ee23btech11217/Prism/PCB/Audio.kicad_sch

## KiCad design PCB/Audio.kicad_sch (2025-03-10, last stored version)

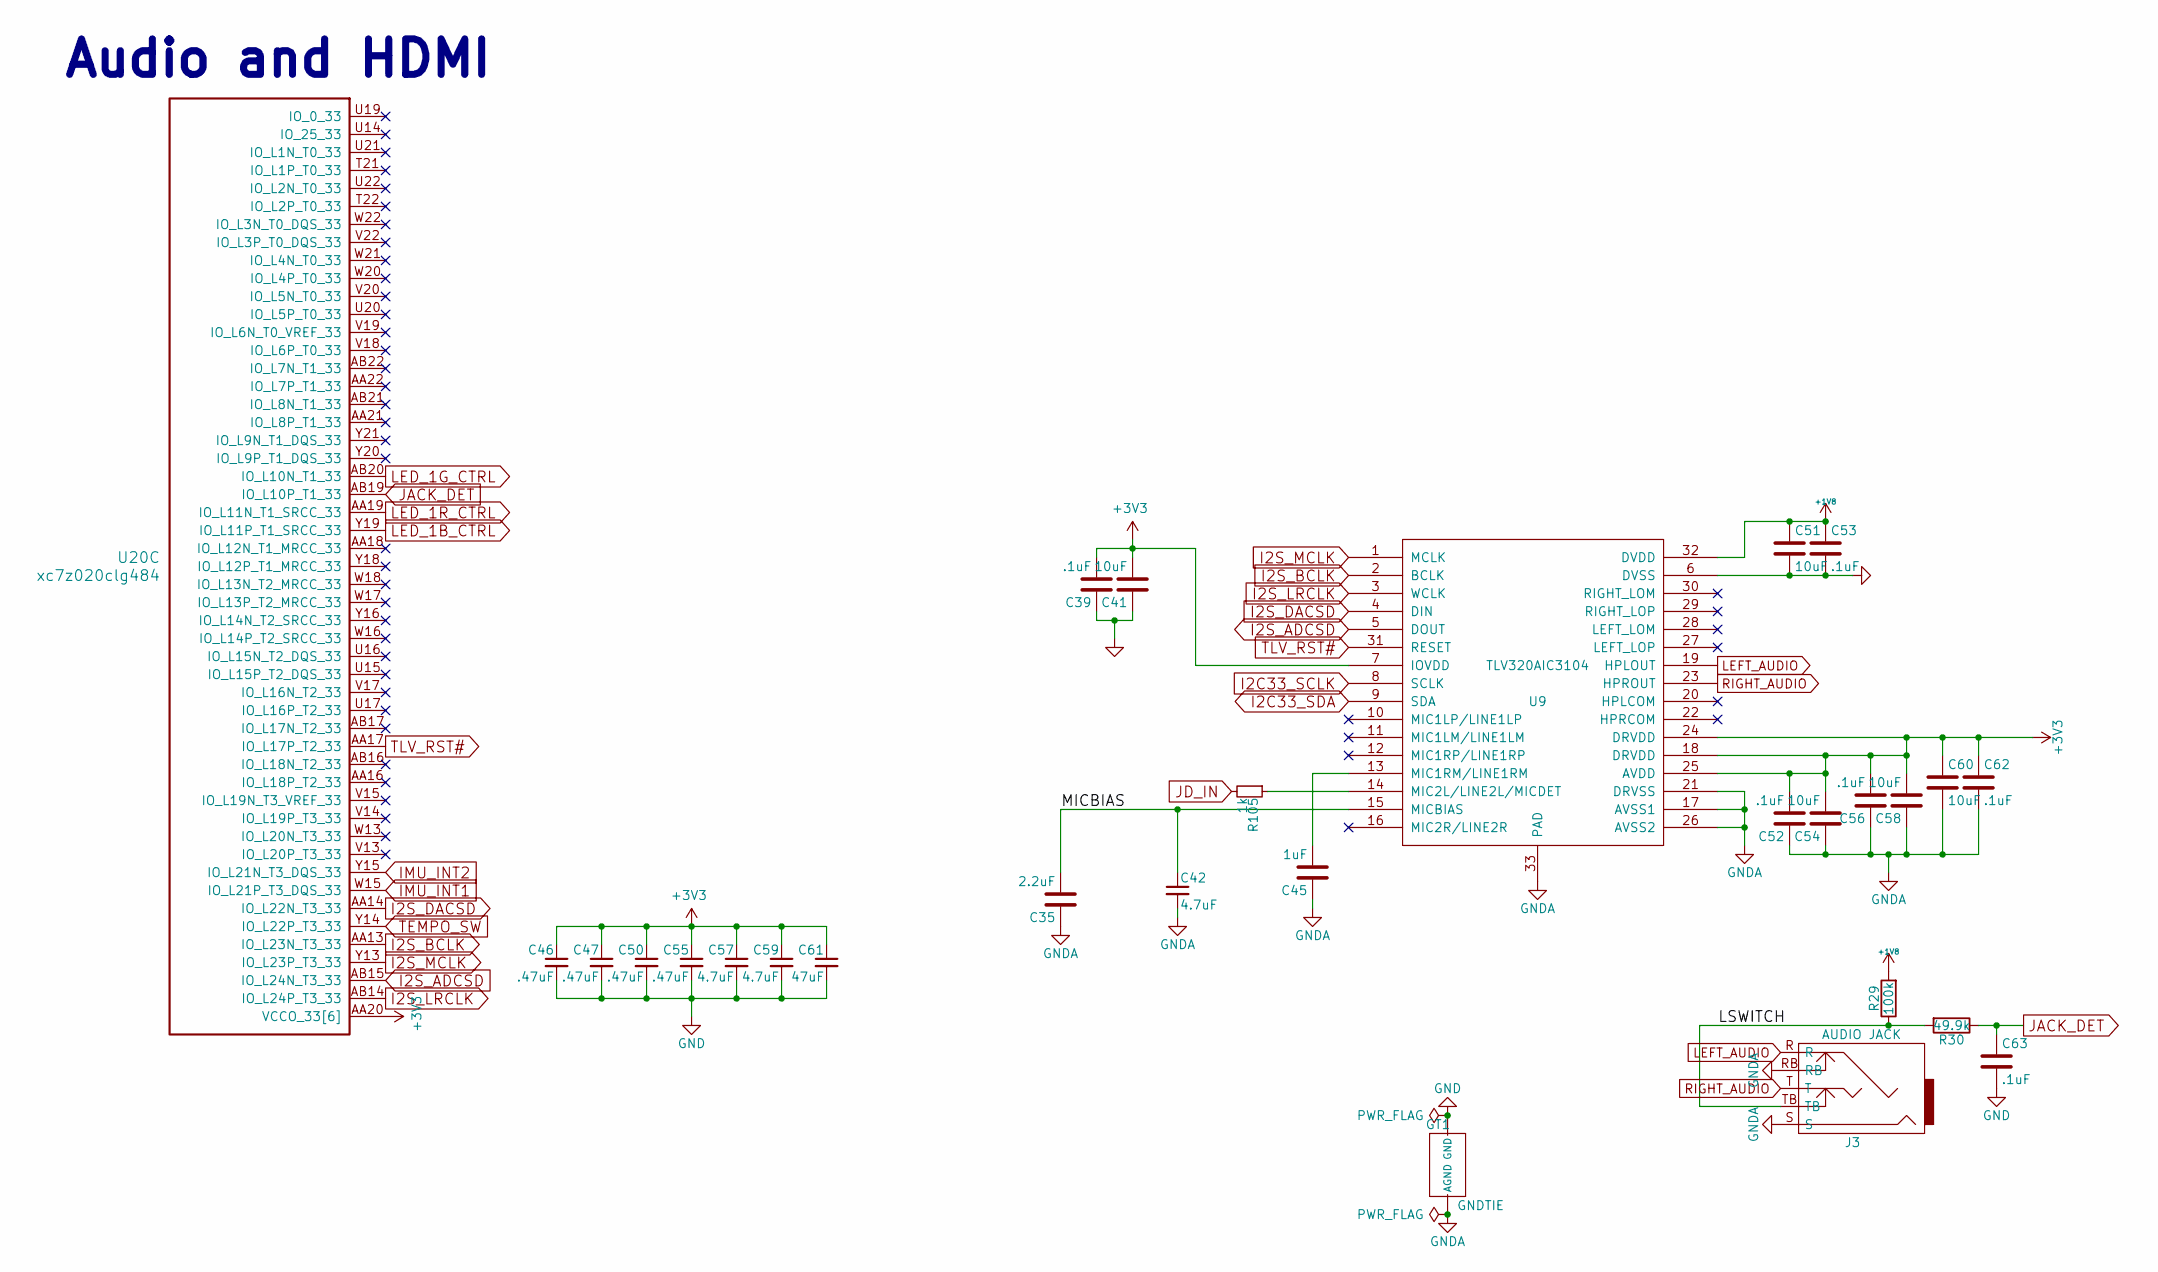
[picture p12: schematic Audio.kicad_sch]

Parts:
C35: 2.2uF; C_0402_1005Metric; MPN GRM155R61A225KE95D
C39, C52, C53, C56, C62, C63: .1uF; C_0402_1005Metric; MPN CC0402KRX7R6BB104
C41, C51, C54, C58, C60: 10uF; C_0603_1608Metric; MPN GRM188R61A106KE69J
C42, C57, C59: 4.7uF; C_0402_1005Metric; MPN GRM155R60G475ME47D
C45: 1uF; C_0402_1005Metric; MPN CC0402KRX5R6BB105
C46, C47, C50, C55: .47uF; C_0402_1005Metric; MPN CC0402KRX5R5BB474
C61: 47uF; C_0805_2012Metric; MPN GRM219R60J476ME44D
GT1: GNDTIE; gndtie
J3: AUDIO JACK; RA49C14B; MPN RA49C12B
R29: 100k; R_0402_1005Metric; MPN RC0402FR-07100KL
R30: 49.9k; R_0402_1005Metric; MPN RC0402FR-0749K9L
R105: 1k; R_0402_1005Metric; MPN RC0402FR-071KL
U9: TLV320AIC3104; QFN-32-1EP_5x5mm_P0.5mm_EP3.65x3.65mm; MPN TLV320AIC3104IRHBR
U20: xc7z020clg484; BGA-484_19.0x19.0mm_Layout22x22_P0.80mm_dia0.40mm

Connections:
+1V8: C51.1, C53.1, R29.2, U9.32 (DVDD)
+3V3: C39.2, C41.2, C46.1, C47.1, C50.1, C52.2, C54.2, C55.1, C56.2, C57.1, C58.2, C59.1, C60.1, C61.1, C62.1, U9.7 (IOVDD), U9.18 (DRVDD), U9.24 (DRVDD), U9.25 (AVDD), U20.AA20 (VCCO_33[6]), U20.AB13 (VCCO_33[6]), U20.U18 (VCCO_33[6]), U20.V21 (VCCO_33[6]), U20.W14 (VCCO_33[6]), U20.Y17 (VCCO_33[6])
GND: C39.1, C41.1, C46.2, C47.2, C50.2, C51.2, C53.2, C55.2, C57.2, C59.2, C61.2, C63.2, GT1.1 (GND), U9.6 (DVSS)
GNDA: C35.1, C42.2, C45.1, C52.1, C54.1, C56.1, C58.1, C60.2, C62.2, GT1.2 (AGND), J3.RB, J3.S, U9.17 (AVSS1), U9.21 (DRVSS), U9.26 (AVSS2), U9.33 (PAD)
I2C33_SCLK: U9.8 (SCLK)
I2C33_SDA: U9.9 (SDA)
I2S_ADCSD: U9.5 (DOUT), U20.AB15 (IO_L24N_T3_33)
I2S_BCLK: U9.2 (BCLK), U20.AA13 (IO_L23N_T3_33)
I2S_DACSD: U9.4 (DIN), U20.AA14 (IO_L22N_T3_33)
I2S_LRCLK: U9.3 (WCLK), U20.AB14 (IO_L24P_T3_33)
I2S_MCLK: U9.1 (MCLK), U20.Y13 (IO_L23P_T3_33)
IMU_INT1: U20.W15 (IO_L21P_T3_DQS_33)
IMU_INT2: U20.Y15 (IO_L21N_T3_DQS_33)
JACK_DET: C63.1, R30.1, U20.AB19 (IO_L10P_T1_33)
JD_IN: R105.2
LED_1B_CTRL: U20.Y19 (IO_L11P_T1_SRCC_33)
LED_1G_CTRL: U20.AB20 (IO_L10N_T1_33)
LED_1R_CTRL: U20.AA19 (IO_L11N_T1_SRCC_33)
LEFT_AUDIO: J3.R, U9.19 (HPLOUT)
LSWITCH: J3.TB, R29.1, R30.2
MICBIAS: C35.2, C42.1, U9.15 (MICBIAS)
unnamed: C45.2, U9.13 (MIC1RM/LINE1RM)
unnamed: R105.1, U9.14 (MIC2L/LINE2L/MICDET)
RIGHT_AUDIO: J3.T, U9.23 (HPROUT)
TEMPO_SW: U20.Y14 (IO_L22P_T3_33)
TLV_RST#: U9.31 (RESET), U20.AA17 (IO_L17P_T2_33)

Notes on the sheet:
Audio and HDMI
