ee23btech11217/Prism/PCB/DDR3.kicad_sch

## KiCad design PCB/DDR3.kicad_sch (2025-03-09, last stored version)

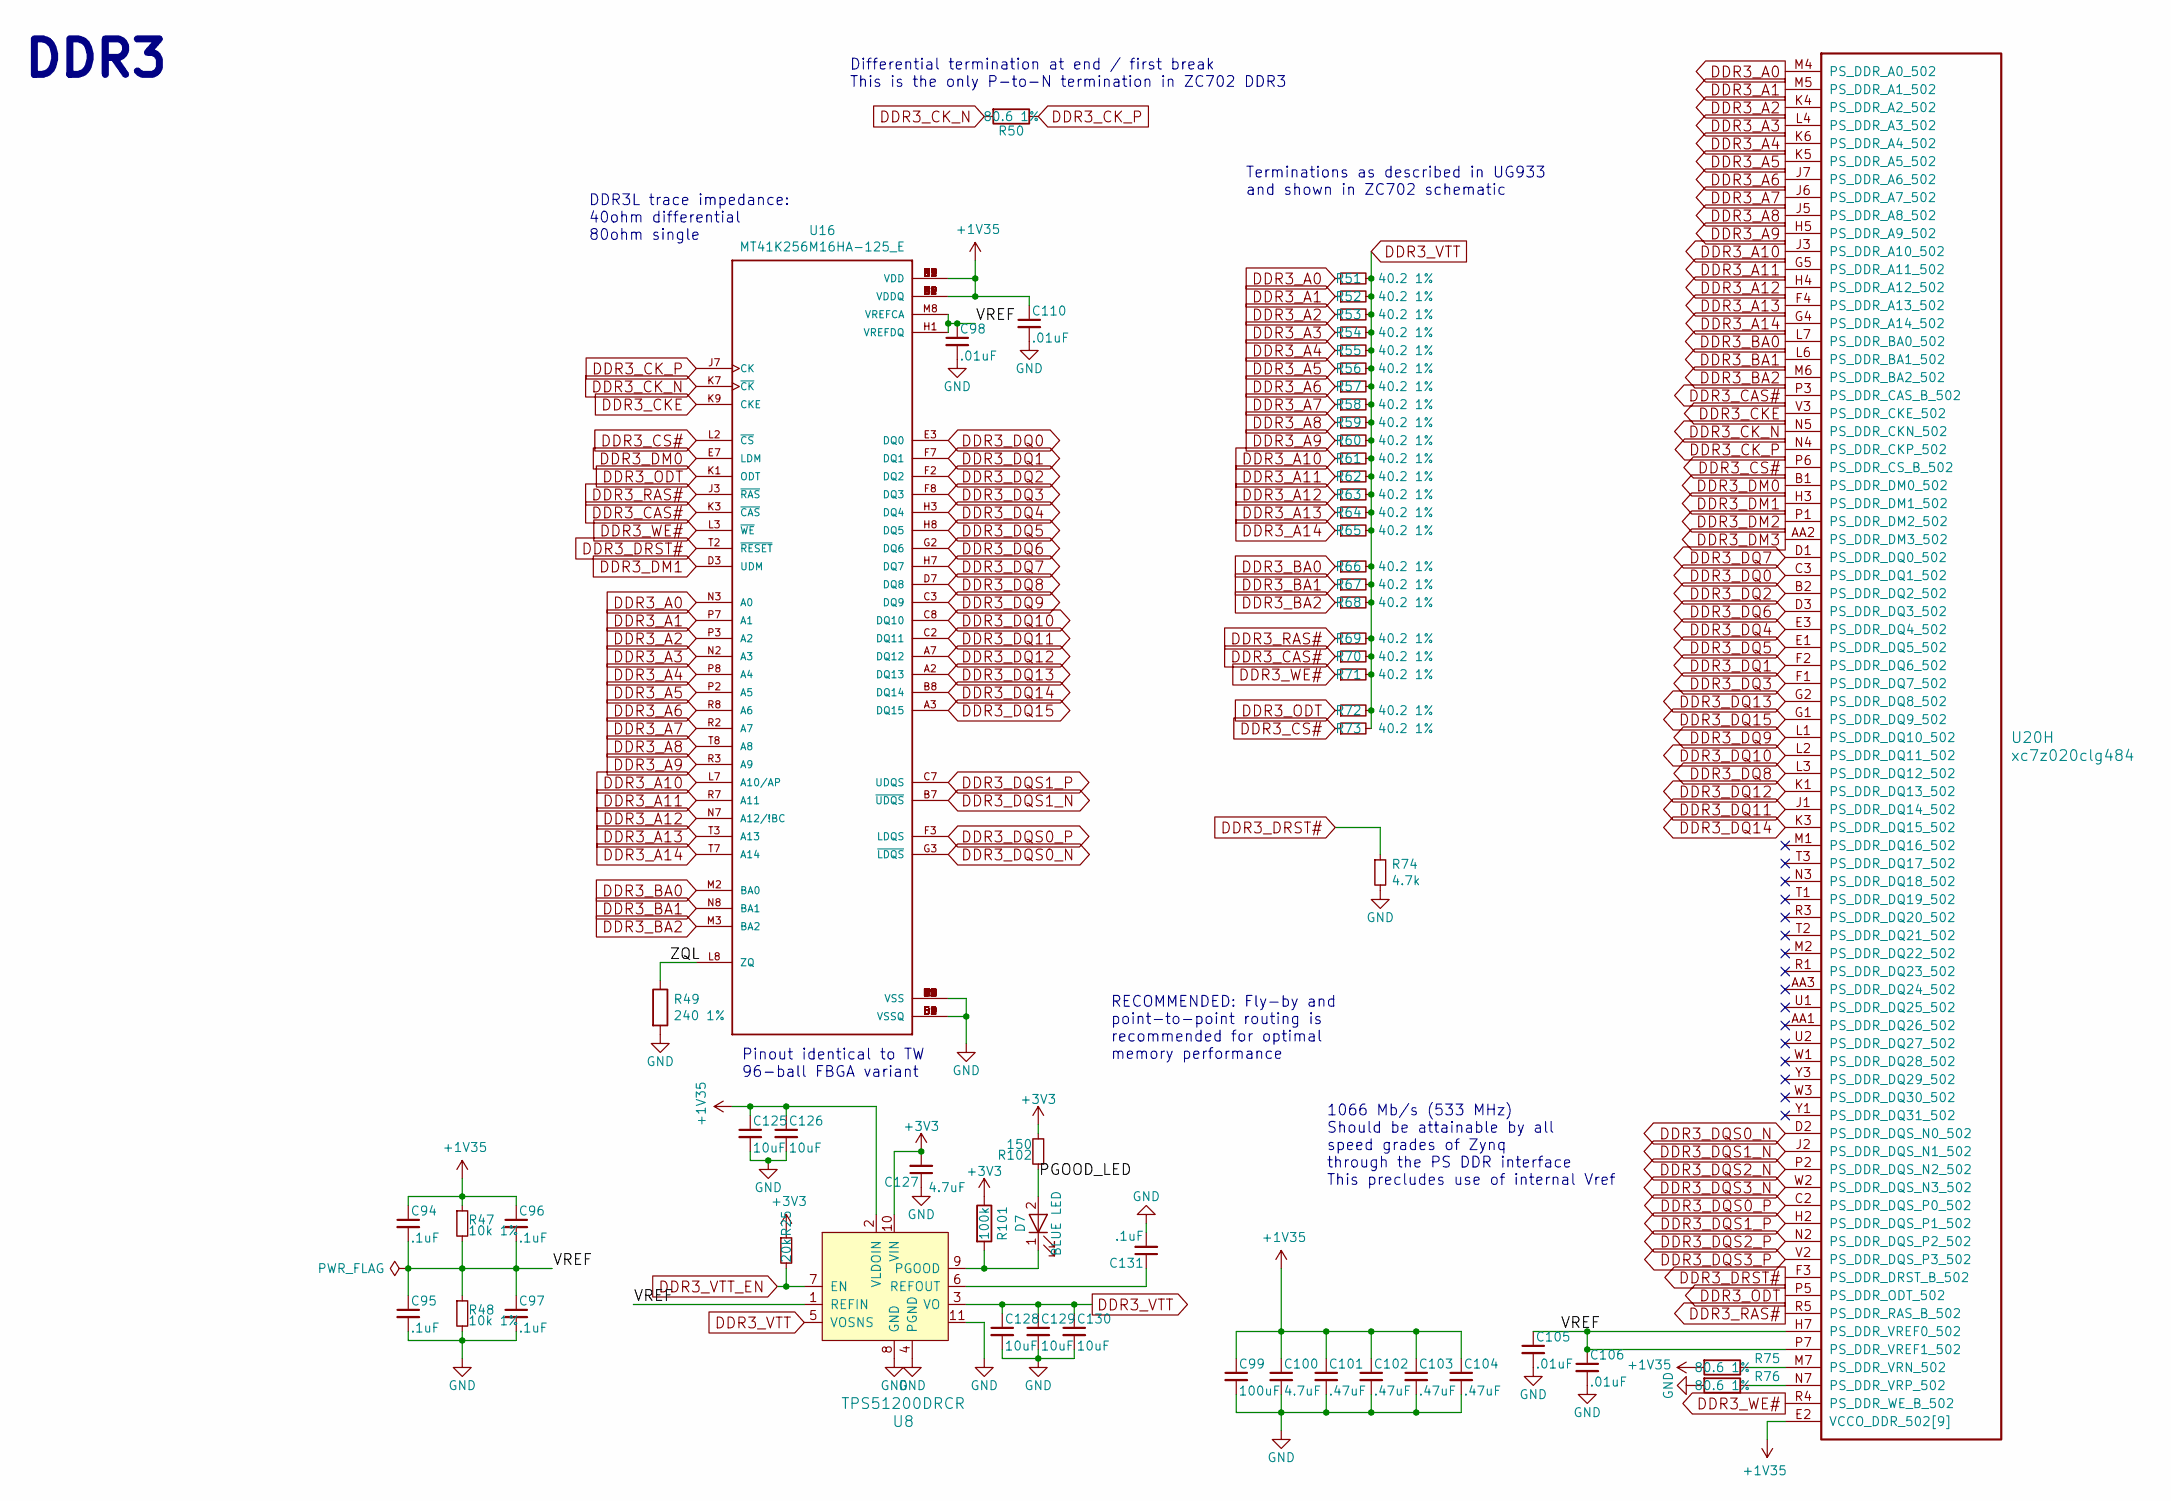
[picture p13: schematic DDR3.kicad_sch]

Parts:
C94, C95, C96, C97, C131: .1uF; C_0402_1005Metric; MPN CC0402KRX7R6BB104
C98, C105, C106, C110: .01uF; C_0402_1005Metric; MPN GRM155R71H103KA88J
C99: 100uF; C_1210_3225Metric; MPN JMK325ABJ107MM-P
C100, C127: 4.7uF; C_0402_1005Metric; MPN GRM155R60G475ME47D
C101, C102, C103, C104: .47uF; C_0402_1005Metric; MPN CC0402KRX5R5BB474
C125, C126, C128, C129, C130: 10uF; C_0603_1608Metric; MPN GRM188R61A106KE69J
D7: BLUE LED; C_0603_1608Metric; MPN VLMB1300-GS08
R25: 20k; R_0402_1005Metric; MPN RT0402BRD0720KL
R47, R48: 10k 1%; R_0402_1005Metric; MPN RC0402FR-0710KL
R49: 240 1%; R_0402_1005Metric; MPN RC0402FR-07240RL
R50, R75, R76: 80.6 1%; R_0402_1005Metric; MPN RC0402FR-0780R6L
R51, R52, R53, R54, R55, R56, R57, R58, R59, R60, R61, R62, R63, R64, R65, R66, R67, R68, R69, R70, R71, R72, R73: 40.2 1%; R_0402_1005Metric; MPN RC0402FR-0740R2L
R74: 4.7k; R_0402_1005Metric; MPN RC0402JR-074K7L
R101: 100k; R_0402_1005Metric; MPN RC0402FR-07100KL
R102: 150; R_0402_1005Metric; MPN RC0402FR-07150RL
U8: TPS51200DRCR; VSON-10-1EP_3x3mm_P0.5mm_EP1.65x2.4mm_ThermalVias; MPN TPS51200DRCR; Digi-Key_PN 296-26978-1-ND
U16: MT41K256M16HA-125_E; FBGA-96-DDR3-SDRAM; MPN MT41K256M16TW-107
U20: xc7z020clg484; BGA-484_19.0x19.0mm_Layout22x22_P0.80mm_dia0.40mm

Connections:
+1V35: C94.1, C96.1, C99.1, C100.1, C101.1, C102.1, C103.1, C104.1, C110.1, C125.1, C126.1, R47.1, R75.2, U8.2 (VLDOIN), U16.A1 (VDDQ), U16.A8 (VDDQ), U16.B2 (VDD), U16.C1 (VDDQ), U16.C9 (VDDQ), U16.D2 (VDDQ), U16.D9 (VDD), U16.E9 (VDDQ), U16.F1 (VDDQ), U16.G7 (VDD), U16.H2 (VDDQ), U16.H9 (VDDQ), U16.K2 (VDD), U16.K8 (VDD), U16.N1 (VDD), U16.N9 (VDD), U16.R1 (VDD), U16.R9 (VDD), U20.E2 (VCCO_DDR_502[9]), U20.F5 (VCCO_DDR_502[9]), U20.H1 (VCCO_DDR_502[9]), U20.J4 (VCCO_DDR_502[9]), U20.K7 (VCCO_DDR_502[9]), U20.M3 (VCCO_DDR_502[9]), U20.N6 (VCCO_DDR_502[9]), U20.R2 (VCCO_DDR_502[9]), U20.V1 (VCCO_DDR_502[9])
+3V3: C127.2, R25.1, R101.1, R102.2, U8.10 (VIN)
DDR3_A0: R51.1, U16.N3 (A0), U20.M4 (PS_DDR_A0_502)
DDR3_A1: R52.1, U16.P7 (A1), U20.M5 (PS_DDR_A1_502)
DDR3_A2: R53.1, U16.P3 (A2), U20.K4 (PS_DDR_A2_502)
DDR3_A3: R54.1, U16.N2 (A3), U20.L4 (PS_DDR_A3_502)
DDR3_A4: R55.1, U16.P8 (A4), U20.K6 (PS_DDR_A4_502)
DDR3_A5: R56.1, U16.P2 (A5), U20.K5 (PS_DDR_A5_502)
DDR3_A6: R57.1, U16.R8 (A6), U20.J7 (PS_DDR_A6_502)
DDR3_A7: R58.1, U16.R2 (A7), U20.J6 (PS_DDR_A7_502)
DDR3_A8: R59.1, U16.T8 (A8), U20.J5 (PS_DDR_A8_502)
DDR3_A9: R60.1, U16.R3 (A9), U20.H5 (PS_DDR_A9_502)
DDR3_A10: R61.1, U16.L7 (A10/AP), U20.J3 (PS_DDR_A10_502)
DDR3_A11: R62.1, U16.R7 (A11), U20.G5 (PS_DDR_A11_502)
DDR3_A12: R63.1, U16.N7 (A12/!BC), U20.H4 (PS_DDR_A12_502)
DDR3_A13: R64.1, U16.T3 (A13), U20.F4 (PS_DDR_A13_502)
DDR3_A14: R65.1, U16.T7 (A14), U20.G4 (PS_DDR_A14_502)
DDR3_BA0: R66.1, U16.M2 (BA0), U20.L7 (PS_DDR_BA0_502)
DDR3_BA1: R67.1, U16.N8 (BA1), U20.L6 (PS_DDR_BA1_502)
DDR3_BA2: R68.1, U16.M3 (BA2), U20.M6 (PS_DDR_BA2_502)
DDR3_CAS#: R70.1, U16.K3 (~CAS), U20.P3 (PS_DDR_CAS_B_502)
DDR3_CKE: U16.K9 (CKE), U20.V3 (PS_DDR_CKE_502)
DDR3_CK_N: R50.2, U16.K7 (~CK), U20.N5 (PS_DDR_CKN_502)
DDR3_CK_P: R50.1, U16.J7 (CK), U20.N4 (PS_DDR_CKP_502)
DDR3_CS#: R73.1, U16.L2 (~CS), U20.P6 (PS_DDR_CS_B_502)
DDR3_DM0: U16.E7 (LDM), U20.B1 (PS_DDR_DM0_502)
DDR3_DM1: U16.D3 (UDM), U20.H3 (PS_DDR_DM1_502)
DDR3_DM2: U20.P1 (PS_DDR_DM2_502)
DDR3_DM3: U20.AA2 (PS_DDR_DM3_502)
DDR3_DQ0: U16.E3 (DQ0), U20.C3 (PS_DDR_DQ1_502)
DDR3_DQ1: U16.F7 (DQ1), U20.F2 (PS_DDR_DQ6_502)
DDR3_DQ2: U16.F2 (DQ2), U20.B2 (PS_DDR_DQ2_502)
DDR3_DQ3: U16.F8 (DQ3), U20.F1 (PS_DDR_DQ7_502)
DDR3_DQ4: U16.H3 (DQ4), U20.E3 (PS_DDR_DQ4_502)
DDR3_DQ5: U16.H8 (DQ5), U20.E1 (PS_DDR_DQ5_502)
DDR3_DQ6: U16.G2 (DQ6), U20.D3 (PS_DDR_DQ3_502)
DDR3_DQ7: U16.H7 (DQ7), U20.D1 (PS_DDR_DQ0_502)
DDR3_DQ8: U16.D7 (DQ8), U20.L3 (PS_DDR_DQ12_502)
DDR3_DQ9: U16.C3 (DQ9), U20.L1 (PS_DDR_DQ10_502)
DDR3_DQ10: U16.C8 (DQ10), U20.L2 (PS_DDR_DQ11_502)
DDR3_DQ11: U16.C2 (DQ11), U20.J1 (PS_DDR_DQ14_502)
DDR3_DQ12: U16.A7 (DQ12), U20.K1 (PS_DDR_DQ13_502)
DDR3_DQ13: U16.A2 (DQ13), U20.G2 (PS_DDR_DQ8_502)
DDR3_DQ14: U16.B8 (DQ14), U20.K3 (PS_DDR_DQ15_502)
DDR3_DQ15: U16.A3 (DQ15), U20.G1 (PS_DDR_DQ9_502)
DDR3_DQS0_N: U16.G3 (~LDQS), U20.D2 (PS_DDR_DQS_N0_502)
DDR3_DQS0_P: U16.F3 (LDQS), U20.C2 (PS_DDR_DQS_P0_502)
DDR3_DQS1_N: U16.B7 (~UDQS), U20.J2 (PS_DDR_DQS_N1_502)
DDR3_DQS1_P: U16.C7 (UDQS), U20.H2 (PS_DDR_DQS_P1_502)
DDR3_DQS2_N: U20.P2 (PS_DDR_DQS_N2_502)
DDR3_DQS2_P: U20.N2 (PS_DDR_DQS_P2_502)
DDR3_DQS3_N: U20.W2 (PS_DDR_DQS_N3_502)
DDR3_DQS3_P: U20.V2 (PS_DDR_DQS_P3_502)
DDR3_DRST#: R74.1, U16.T2 (~RESET), U20.F3 (PS_DDR_DRST_B_502)
DDR3_ODT: R72.1, U16.K1 (ODT), U20.P5 (PS_DDR_ODT_502)
DDR3_RAS#: R69.1, U16.J3 (~RAS), U20.R5 (PS_DDR_RAS_B_502)
DDR3_VTT: C128.1, C129.1, C130.1, R51.2, R52.2, R53.2, R54.2, R55.2, R56.2, R57.2, R58.2, R59.2, R60.2, R61.2, R62.2, R63.2, R64.2, R65.2, R66.2, R67.2, R68.2, R69.2, R70.2, R71.2, R72.2, R73.2, U8.3 (VO), U8.5 (VOSNS)
DDR3_VTT_EN: R25.2, U8.7 (EN)
DDR3_WE#: R71.1, U16.L3 (~WE), U20.R4 (PS_DDR_WE_B_502)
GND: C95.2, C97.2, C98.2, C99.2, C100.2, C101.2, C102.2, C103.2, C104.2, C105.2, C106.2, C110.2, C125.2, C126.2, C127.1, C128.2, C129.2, C130.2, C131.2, R48.2, R49.2, R74.2, R76.2, U8.4 (PGND), U8.8 (GND), U8.11, U16.A9 (VSS), U16.B1 (VSSQ), U16.B3 (VSS), U16.B9 (VSSQ), U16.D1 (VSSQ), U16.D8 (VSSQ), U16.E1 (VSS), U16.E2 (VSSQ), U16.E8 (VSSQ), U16.F9 (VSSQ), U16.G1 (VSSQ), U16.G8 (VSS), U16.G9 (VSSQ), U16.J2 (VSS), U16.J8 (VSS), U16.M1 (VSS), U16.M9 (VSS), U16.P1 (VSS), U16.P9 (VSS), U16.T1 (VSS), U16.T9 (VSS)
unnamed: C131.1, U8.6 (REFOUT)
unnamed: D7.1 (K), R101.2, U8.9 (PGOOD)
unnamed: R75.1, U20.M7 (PS_DDR_VRN_502)
unnamed: R76.1, U20.N7 (PS_DDR_VRP_502)
PGOOD_LED: D7.2 (A), R102.1
VREF: C94.2, C95.1, C96.2, C97.1, C98.1, C105.1, C106.1, R47.2, R48.1, U8.1 (REFIN), U16.H1 (VREFDQ), U16.M8 (VREFCA), U20.H7 (PS_DDR_VREF0_502), U20.P7 (PS_DDR_VREF1_502)
ZQL: R49.1, U16.L8 (ZQ)

Notes on the sheet:
Terminations as described in UG933 and shown in ZC702 schematic
Pinout identical to TW 96-ball FBGA variant
DDR3
1066 Mb/s (533 MHz) Should be attainable by all speed grades of Zynq through the PS DDR interface This precludes use of internal Vref
Differential termination at end / first break This is the only P-to-N termination in ZC702 DDR3
DDR3L trace impedance: 40ohm differential 80ohm single
RECOMMENDED: Fly-by and point-to-point routing is recommended for optimal memory performance
