ee23btech11217/Prism/PCB/DDR.kicad_sch

## KiCad design PCB/DDR.kicad_sch (2025-03-01, last stored version)

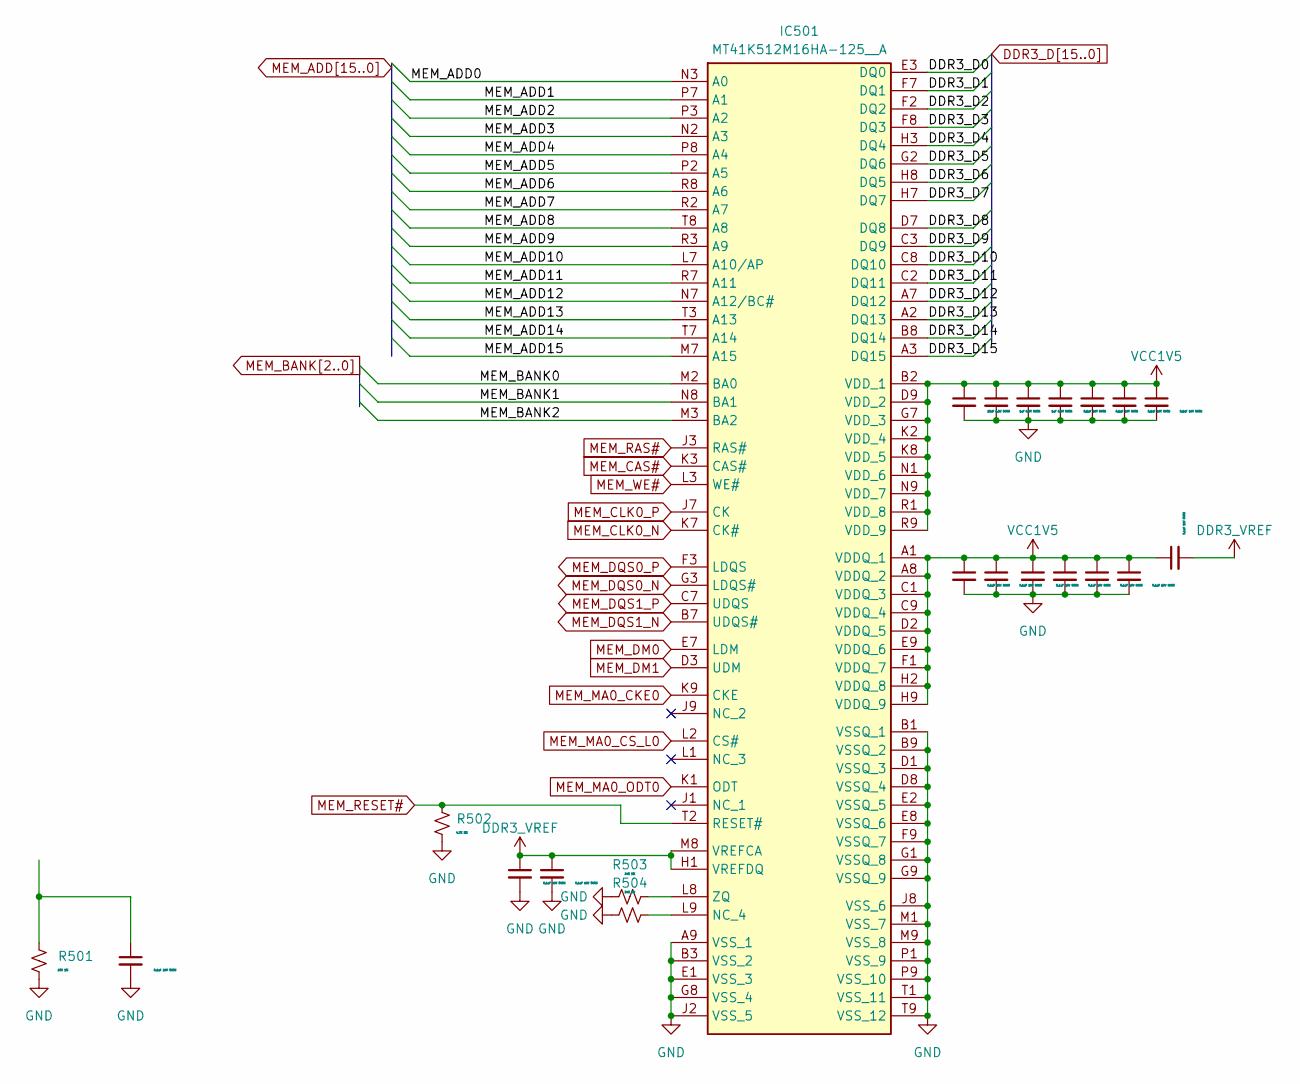
[picture p14: schematic DDR.kicad_sch]

Parts:
C501, C502, C503, C505, C507, C509, C510, C511, C512, C513, C514, C515, C516, C517: 0.1uF 16V 0805; C_0805_2012Metric
C504: 10uF 6.3V 0805; C_0805_2012Metric
C506, C508: 1uF 6.3V 0805; C_0805_2012Metric
IC501: MT41K512M16HA-125__A; BGA96C80P9X16_900X1400X120; Mouser Part Number 913-41K512M16HA125A
R501: 10K 1%; R_0805_2012Metric
R502: 4.7K 5%; R_0805_2012Metric
R503, R504: 240 5%; R_0805_2012Metric

Connections:
DDR3_D0: IC501.E3 (DQ0)
DDR3_D1: IC501.F7 (DQ1)
DDR3_D2: IC501.F2 (DQ2)
DDR3_D3: IC501.F8 (DQ3)
DDR3_D4: IC501.H3 (DQ4)
DDR3_D5: IC501.G2 (DQ6)
DDR3_D6: IC501.H8 (DQ5)
DDR3_D7: IC501.H7 (DQ7)
DDR3_D8: IC501.D7 (DQ8)
DDR3_D9: IC501.C3 (DQ9)
DDR3_D10: IC501.C8 (DQ10)
DDR3_D11: IC501.C2 (DQ11)
DDR3_D12: IC501.A7 (DQ12)
DDR3_D13: IC501.A2 (DQ13)
DDR3_D14: IC501.B8 (DQ14)
DDR3_D15: IC501.A3 (DQ15)
DDR3_VREF: C502.1, C503.1, C517.2, IC501.H1 (VREFDQ), IC501.M8 (VREFCA)
GND: C501.2, C502.2, C503.2, C504.2, C505.2, C506.2, C507.2, C508.2, C509.2, C510.2, C511.2, C512.2, C513.2, C514.2, C515.2, C516.2, IC501.A9 (VSS_1), IC501.B1 (VSSQ_1), IC501.B3 (VSS_2), IC501.B9 (VSSQ_2), IC501.D1 (VSSQ_3), IC501.D8 (VSSQ_4), IC501.E1 (VSS_3), IC501.E2 (VSSQ_5), IC501.E8 (VSSQ_6), IC501.F9 (VSSQ_7), IC501.G1 (VSSQ_8), IC501.G8 (VSS_4), IC501.G9 (VSSQ_9), IC501.J2 (VSS_5), IC501.J8 (VSS_6), IC501.M1 (VSS_7), IC501.M9 (VSS_8), IC501.P1 (VSS_9), IC501.P9 (VSS_10), IC501.T1 (VSS_11), IC501.T9 (VSS_12), R501.2, R502.1, R503.2, R504.2
MEM_ADD0: IC501.N3 (A0)
MEM_ADD1: IC501.P7 (A1)
MEM_ADD2: IC501.P3 (A2)
MEM_ADD3: IC501.N2 (A3)
MEM_ADD4: IC501.P8 (A4)
MEM_ADD5: IC501.P2 (A5)
MEM_ADD6: IC501.R8 (A6)
MEM_ADD7: IC501.R2 (A7)
MEM_ADD8: IC501.T8 (A8)
MEM_ADD9: IC501.R3 (A9)
MEM_ADD10: IC501.L7 (A10/AP)
MEM_ADD11: IC501.R7 (A11)
MEM_ADD12: IC501.N7 (A12/BC#)
MEM_ADD13: IC501.T3 (A13)
MEM_ADD14: IC501.T7 (A14)
MEM_ADD15: IC501.M7 (A15)
MEM_BANK0: IC501.M2 (BA0)
MEM_BANK1: IC501.N8 (BA1)
MEM_BANK2: IC501.M3 (BA2)
MEM_CAS#: IC501.K3 (CAS#)
MEM_CLK0_N: IC501.K7 (CK#)
MEM_CLK0_P: IC501.J7 (CK)
MEM_DM0: IC501.E7 (LDM)
MEM_DM1: IC501.D3 (UDM)
MEM_DQS0_N: IC501.G3 (LDQS#)
MEM_DQS0_P: IC501.F3 (LDQS)
MEM_DQS1_N: IC501.B7 (UDQS#)
MEM_DQS1_P: IC501.C7 (UDQS)
MEM_MA0_CKE0: IC501.K9 (CKE)
MEM_MA0_CS_L0: IC501.L2 (CS#)
MEM_MA0_ODT0: IC501.K1 (ODT)
MEM_RAS#: IC501.J3 (RAS#)
MEM_RESET#: IC501.T2 (RESET#), R502.2
MEM_WE#: IC501.L3 (WE#)
unnamed: C501.1, R501.1
unnamed: IC501.L8 (ZQ), R503.1
unnamed: IC501.L9 (NC_4), R504.1
VCC1V5: C504.1, C505.1, C506.1, C507.1, C508.1, C509.1, C510.1, C511.1, C512.1, C513.1, C514.1, C515.1, C516.1, C517.1, IC501.A1 (VDDQ_1), IC501.A8 (VDDQ_2), IC501.B2 (VDD_1), IC501.C1 (VDDQ_3), IC501.C9 (VDDQ_4), IC501.D2 (VDDQ_5), IC501.D9 (VDD_2), IC501.E9 (VDDQ_6), IC501.F1 (VDDQ_7), IC501.G7 (VDD_3), IC501.H2 (VDDQ_8), IC501.H9 (VDDQ_9), IC501.K2 (VDD_4), IC501.K8 (VDD_5), IC501.N1 (VDD_6), IC501.N9 (VDD_7), IC501.R1 (VDD_8), IC501.R9 (VDD_9)
