ee23btech11217/Prism/PCB/LCD50.kicad_sch

## KiCad design PCB/LCD50.kicad_sch (2025-03-09, last stored version)

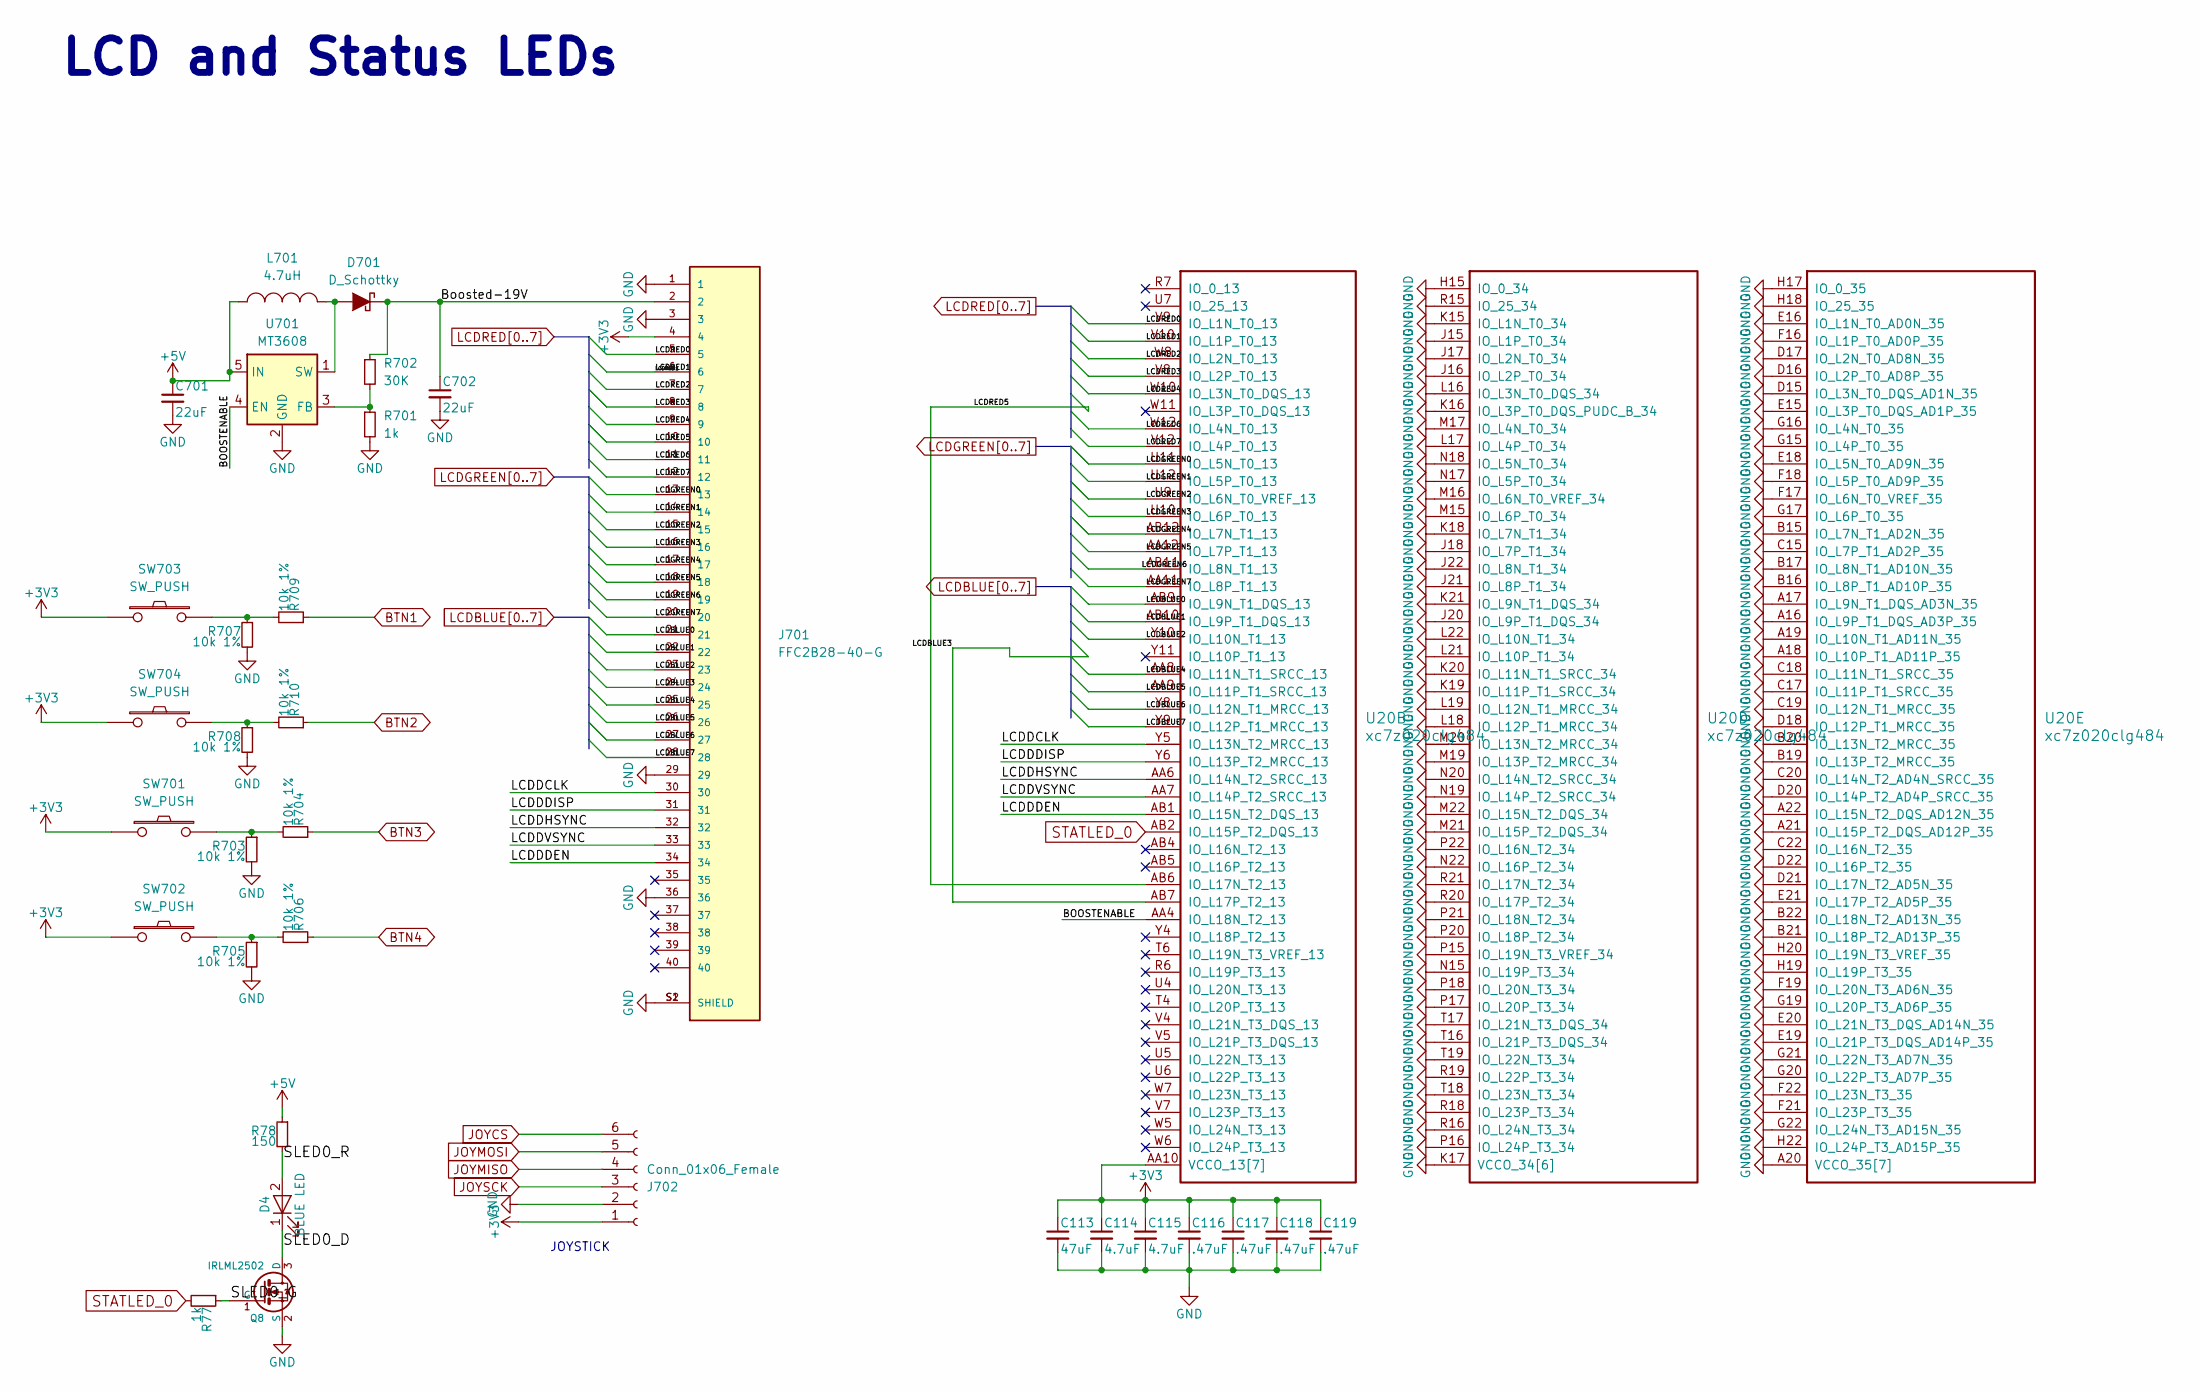
[picture p15: schematic LCD50.kicad_sch]

Parts:
C113: 47uF; C_1210_3225Metric; MPN GRM32ER70J476ME20L
C114, C115: 4.7uF; C_0402_1005Metric; MPN GRM155R60G475ME47D
C116, C117, C118, C119: .47uF; C_0402_1005Metric; MPN CC0402KRX5R5BB474
C701, C702: 22uF; C_0603_1608Metric; MPN CC0402KRX5R5BB474
D4: BLUE LED; C_0603_1608Metric; MPN VLMB1300-GS08
D701: D_Schottky; Nexperia_CFP3_SOD-123W
J701: FFC2B28-40-G; GCT_FFC2B28-40-G; PARTREV A
J702: Conn_01x06_Female; PinSocket_1x06_P2.54mm_Horizontal
L701: 4.7uH; C_1812_4532Metric
Q8: IRLML2502; SOT-23; MPN IRLML2502TRPBF
R77: 1k; R_0402_1005Metric; MPN RC0402FR-071KL
R78: 150; R_0402_1005Metric; MPN RC0402FR-07150RL
R701: 1k; R_0402_1005Metric
R702: 30K; R_0402_1005Metric
R703, R704, R705, R706, R707, R708, R709, R710: 10k 1%; R_0402_1005Metric; MPN RC0402FR-07150RL
SW701, SW702, SW703, SW704: SW_PUSH; SW_SPST_TL3305A
U20: xc7z020clg484; BGA-484_19.0x19.0mm_Layout22x22_P0.80mm_dia0.40mm
U701: MT3608; SOT-23-6

Connections:
+3V3: C113.1, C114.1, C115.1, C116.1, C117.1, C118.1, C119.1, J701.4, J702.1, SW701.1, SW702.1, SW703.1, SW704.1, U20.AA10 (VCCO_13[7]), U20.AB3 (VCCO_13[7]), U20.T5 (VCCO_13[7]), U20.U8 (VCCO_13[7]), U20.V11 (VCCO_13[7]), U20.W4 (VCCO_13[7]), U20.Y7 (VCCO_13[7])
+5V: C701.1, L701.1, R78.1, U701.5 (IN)
BOOSTENABLE: U20.AA4 (IO_L18N_T2_13), U701.4 (EN)
BTN1: R709.1
BTN2: R710.1
BTN3: R704.1
BTN4: R706.1
Boosted-19V: C702.1, D701.1 (K), J701.2, R702.1
GND: C113.2, C114.2, C115.2, C116.2, C117.2, C118.2, C119.2, C701.2, C702.2, J701.1, J701.3, J701.29, J701.36, J701.S1 (SHIELD), J701.S2 (SHIELD), J702.2, Q8.2 (S), R701.2, R703.2, R705.2, R707.2, R708.2, U20.A16 (IO_L9P_T1_DQS_AD3P_35), U20.A17 (IO_L9N_T1_DQS_AD3N_35), U20.A18 (IO_L10P_T1_AD11P_35), U20.A19 (IO_L10N_T1_AD11N_35), U20.A20 (VCCO_35[7]), U20.A21 (IO_L15P_T2_DQS_AD12P_35), U20.A22 (IO_L15N_T2_DQS_AD12N_35), U20.B15 (IO_L7N_T1_AD2N_35), U20.B16 (IO_L8P_T1_AD10P_35), U20.B17 (IO_L8N_T1_AD10N_35), U20.B19 (IO_L13P_T2_MRCC_35), U20.B20 (IO_L13N_T2_MRCC_35), U20.B21 (IO_L18P_T2_AD13P_35), U20.B22 (IO_L18N_T2_AD13N_35), U20.C15 (IO_L7P_T1_AD2P_35), U20.C16 (VCCO_35[7]), U20.C17 (IO_L11P_T1_SRCC_35), U20.C18 (IO_L11N_T1_SRCC_35), U20.C19 (IO_L12N_T1_MRCC_35), U20.C20 (IO_L14N_T2_AD4N_SRCC_35), U20.C22 (IO_L16N_T2_35), U20.D15 (IO_L3N_T0_DQS_AD1N_35), U20.D16 (IO_L2P_T0_AD8P_35), U20.D17 (IO_L2N_T0_AD8N_35), U20.D18 (IO_L12P_T1_MRCC_35), U20.D19 (VCCO_35[7]), U20.D20 (IO_L14P_T2_AD4P_SRCC_35), U20.D21 (IO_L17N_T2_AD5N_35), U20.D22 (IO_L16P_T2_35), U20.E15 (IO_L3P_T0_DQS_AD1P_35), U20.E16 (IO_L1N_T0_AD0N_35), U20.E18 (IO_L5N_T0_AD9N_35), U20.E19 (IO_L21P_T3_DQS_AD14P_35), U20.E20 (IO_L21N_T3_DQS_AD14N_35), U20.E21 (IO_L17P_T2_AD5P_35), U20.E22 (VCCO_35[7]), U20.F15 (VCCO_35[7]), U20.F16 (IO_L1P_T0_AD0P_35), U20.F17 (IO_L6N_T0_VREF_35), U20.F18 (IO_L5P_T0_AD9P_35), U20.F19 (IO_L20N_T3_AD6N_35), U20.F21 (IO_L23P_T3_35), U20.F22 (IO_L23N_T3_35), U20.G15 (IO_L4P_T0_35), U20.G16 (IO_L4N_T0_35), U20.G17 (IO_L6P_T0_35), U20.G18 (VCCO_35[7]), U20.G19 (IO_L20P_T3_AD6P_35), U20.G20 (IO_L22P_T3_AD7P_35), U20.G21 (IO_L22N_T3_AD7N_35), U20.G22 (IO_L24N_T3_AD15N_35), U20.H15 (IO_0_34), U20.H17 (IO_0_35), U20.H18 (IO_25_35), U20.H19 (IO_L19P_T3_35), U20.H20 (IO_L19N_T3_VREF_35), U20.H21 (VCCO_35[7]), U20.H22 (IO_L24P_T3_AD15P_35), U20.J15 (IO_L1P_T0_34), U20.J16 (IO_L2P_T0_34), U20.J17 (IO_L2N_T0_34), U20.J18 (IO_L7P_T1_34), U20.J20 (IO_L9P_T1_DQS_34), U20.J21 (IO_L8P_T1_34), U20.J22 (IO_L8N_T1_34), U20.K15 (IO_L1N_T0_34), U20.K16 (IO_L3P_T0_DQS_PUDC_B_34), U20.K17 (VCCO_34[6]), U20.K18 (IO_L7N_T1_34), U20.K19 (IO_L11P_T1_SRCC_34), U20.K20 (IO_L11N_T1_SRCC_34), U20.K21 (IO_L9N_T1_DQS_34), U20.L16 (IO_L3N_T0_DQS_34), U20.L17 (IO_L4P_T0_34), U20.L18 (IO_L12P_T1_MRCC_34), U20.L19 (IO_L12N_T1_MRCC_34), U20.L20 (VCCO_34[6]), U20.L21 (IO_L10P_T1_34), U20.L22 (IO_L10N_T1_34), U20.M15 (IO_L6P_T0_34), U20.M16 (IO_L6N_T0_VREF_34), U20.M17 (IO_L4N_T0_34), U20.M19 (IO_L13P_T2_MRCC_34), U20.M20 (IO_L13N_T2_MRCC_34), U20.M21 (IO_L15P_T2_DQS_34), U20.M22 (IO_L15N_T2_DQS_34), U20.N15 (IO_L19P_T3_34), U20.N16 (VCCO_34[6]), U20.N17 (IO_L5P_T0_34), U20.N18 (IO_L5N_T0_34), U20.N19 (IO_L14P_T2_SRCC_34), U20.N20 (IO_L14N_T2_SRCC_34), U20.N22 (IO_L16P_T2_34), U20.P15 (IO_L19N_T3_VREF_34), U20.P16 (IO_L24P_T3_34), U20.P17 (IO_L20P_T3_34), U20.P18 (IO_L20N_T3_34), U20.P19 (VCCO_34[6]), U20.P20 (IO_L18P_T2_34), U20.P21 (IO_L18N_T2_34), U20.P22 (IO_L16N_T2_34), U20.R15 (IO_25_34), U20.R16 (IO_L24N_T3_34), U20.R18 (IO_L23P_T3_34), U20.R19 (IO_L22P_T3_34), U20.R20 (IO_L17P_T2_34), U20.R21 (IO_L17N_T2_34), U20.R22 (VCCO_34[6]), U20.T15 (VCCO_34[6]), U20.T16 (IO_L21P_T3_DQS_34), U20.T17 (IO_L21N_T3_DQS_34), U20.T18 (IO_L23N_T3_34), U20.T19 (IO_L22N_T3_34), U701.2 (GND)
JOYCS: J702.6
JOYMISO: J702.4
JOYMOSI: J702.5
JOYSCK: J702.3
LCDBLUE0: J701.21, U20.AB9 (IO_L9N_T1_DQS_13)
LCDBLUE1: J701.22, U20.AB10 (IO_L9P_T1_DQS_13)
LCDBLUE2: J701.23, U20.Y10 (IO_L10N_T1_13)
LCDBLUE3: J701.24, U20.AB7 (IO_L17P_T2_13)
LCDBLUE4: J701.25, U20.AA8 (IO_L11N_T1_SRCC_13)
LCDBLUE5: J701.26, U20.AA9 (IO_L11P_T1_SRCC_13)
LCDBLUE6: J701.27, U20.Y8 (IO_L12N_T1_MRCC_13)
LCDBLUE7: J701.28, U20.Y9 (IO_L12P_T1_MRCC_13)
LCDDCLK: J701.30, U20.Y5 (IO_L13N_T2_MRCC_13)
LCDDDEN: J701.34, U20.AB1 (IO_L15N_T2_DQS_13)
LCDDDISP: J701.31, U20.Y6 (IO_L13P_T2_MRCC_13)
LCDDHSYNC: J701.32, U20.AA6 (IO_L14N_T2_SRCC_13)
LCDDVSYNC: J701.33, U20.AA7 (IO_L14P_T2_SRCC_13)
LCDGREEN0: J701.13, U20.U11 (IO_L5N_T0_13)
LCDGREEN1: J701.14, U20.U12 (IO_L5P_T0_13)
LCDGREEN2: J701.15, U20.U9 (IO_L6N_T0_VREF_13)
LCDGREEN3: J701.16, U20.U10 (IO_L6P_T0_13)
LCDGREEN4: J701.17, U20.AB12 (IO_L7N_T1_13)
LCDGREEN5: J701.18, U20.AA12 (IO_L7P_T1_13)
LCDGREEN6: J701.19, U20.AB11 (IO_L8N_T1_13)
LCDGREEN7: J701.20, U20.AA11 (IO_L8P_T1_13)
LCDRED0: J701.5, U20.V9 (IO_L1N_T0_13)
LCDRED1: J701.6, U20.V10 (IO_L1P_T0_13)
LCDRED2: J701.7, U20.W8 (IO_L2N_T0_13)
LCDRED3: J701.8, U20.V8 (IO_L2P_T0_13)
LCDRED4: J701.9, U20.W10 (IO_L3N_T0_DQS_13)
LCDRED5: J701.10, U20.AB6 (IO_L17N_T2_13)
LCDRED6: J701.11, U20.W12 (IO_L4N_T0_13)
LCDRED7: J701.12, U20.V12 (IO_L4P_T0_13)
unnamed: D701.2 (A), L701.2, U701.1 (SW)
unnamed: R701.1, R702.2, U701.3 (FB)
unnamed: R703.1, R704.2, SW701.2
unnamed: R705.1, R706.2, SW702.2
unnamed: R707.1, R709.2, SW703.2
unnamed: R708.1, R710.2, SW704.2
SLED0_D: D4.1 (K), Q8.3 (D)
SLED0_G: Q8.1 (G), R77.1
SLED0_R: D4.2 (A), R78.2
STATLED_0: R77.2, U20.AB2 (IO_L15P_T2_DQS_13)

Notes on the sheet:
JOYSTICK
LCD and Status LEDs
