ee23btech11217/Prism/PCB/Power_management.kicad_sch

## KiCad design PCB/Power_management.kicad_sch (2025-03-09, last stored version)

Schematic: Power_management.kicad_sch

Parts:
C401, C402, C434, C435, C436, C438: 22uF 6.3V 0805; C_0805_2012Metric
C403, C404, C405, C414: 47uF 6.3V 0805; C_0805_2012Metric
C406: 1500pF 50V 0603; C_0603_1608Metric
C407, C409, C411, C413: 10pF 50V 0603; C_0603_1608Metric
C408: 150pF 50V 0603; C_0603_1608Metric
C410: 330pF 50V 0603; C_0603_1608Metric
C412: 1200pF 50V 0603; C_0603_1608Metric
C415, C416, C417, C418: 33nF 16V 0603; C_0603_1608Metric
C419, C448, C450: 1uF 6.3V; C_0805_2012Metric
C420: 10uF 6.3V 0805; C_0805_2012Metric
C421: 0.1uF 25V 0603; C_0603_1608Metric
C422: 4.7uF 16V; C_0805_2012Metric
C423: 3.3uF 16V; C_0805_2012Metric
C424, C425: 0.1uF 25V 0805; C_0805_2012Metric
C426: 10uF 25V 0805; C_0805_2012Metric
C427, C428, C429: 0.01uF 25V 0805; C_0805_2012Metric
C430, C431, C432, C433, C437, C443, C444, C446: 0.1uF 16V 0805; C_0805_2012Metric
C439: 1uF 6.3V 0805; C_0805_2012Metric
C440: 0.1uF16V 0805; C_0805_2012Metric
C441: 22uF 25V 0805; C_0805_2012Metric
C442: 3300pF 50V 0805; C_0805_2012Metric
C445: 22uF 6.3V; C_0805_2012Metric
C447: 1uF6.3V; C_0805_2012Metric
C449, C451: 0.1uF16V; C_0805_2012Metric
FB401: 70 Ohm 100MHz 3A; L_0603_1608Metric
J401: PJ-037AH; CUI_PJ-037AH; PARTREV 1.07
L401, L402, L404, L406, L408: 2.2uH 8A; L_1806_4516Metric
L403, L407: 4.7uH 3A; L_1806_4516Metric
L405: 3.3uH 3A; L_1806_4516Metric
L409: 2.2uH 3A; L_1806_4516Metric
LED401: SML-LX1206SRC-TR; LED_3P2X1P5_LUM
Q401, Q404, Q405: 2N7002E; SOT-23
Q402: PMBT3904YS; SOT-363_SC-70-6
Q403, Q407: 2N3906; TO-92_Inline
Q406: AP2307GN; SOT-23
R401: 33K 1%; R_0805_2012Metric
R402: 100K 1%; R_0805_2012Metric
R403: 180K 1%; R_0805_2012Metric
R404: 75K 1%; R_0805_2012Metric
R405, R407, R421, R425, R426, R427, R429, R432, R433, R434, R435, R437, R438: 10K 1%; R_0805_2012Metric
R406: 150K 1%; R_0805_2012Metric
R408, R409, R410, R411: 0 5%; R_0805_2012Metric
R412, R436, R439: 20K 1%; R_0805_2012Metric
R413: 16K 1%; R_0805_2012Metric
R414: 9.31K 1%; R_0805_2012Metric
R415: 3.01K 1%; R_0805_2012Metric
R416: 8.87K 1%; R_0805_2012Metric
R417: 10.2K 1%; R_0805_2012Metric
R418: 8.2K 5%; R_0805_2012Metric
R419: 100 1%; R_0805_2012Metric
R420: 30K 1%; R_0805_2012Metric
R422: 330 1%; R_0805_2012Metric
R423, R424: 0 /X; R_0805_2012Metric
R428: 100k 1%; R_0805_2012Metric
R430: 69.8K 1%; R_0805_2012Metric
R431: 13.3K 1%; R_0805_2012Metric
SW401: SW_Wuerth_450301014042; SW_SPST_CK_KMS2xxGP
U401: TPS65400RGZR; RGZ0048B
U402: TLV62130RGTR; RGT0016C
U403: LP5907MFX-3.3; SOT-23-5
U404: REF3012; SOT-23

Connections:
AVCC3V3: C450.1, U403.5 (OUT)
CE: U401.23 (CE)
EN_1: Q405.3 (D), R436.1, R437.2, U401.13 (ENSW2), U401.27 (ENSW3), U401.34 (ENSW4), U401.48 (ENSW1_ENSEQ)
EN_6213: U402.13 (EN)
EN_MAIN: Q404.1 (G), R425.2, R438.1, R439.2
GND: C401.2, C402.2, C403.2, C404.2, C405.2, C406.2, C407.2, C408.2, C409.2, C410.2, C411.2, C412.2, C413.2, C414.2, C415.2, C416.2, C417.2, C418.2, C419.2, C420.2, C422.1, C423.1, C431.2, C432.2, C433.2, C434.2, C435.2, C436.2, C439.2, C440.2, C441.2, C442.1, C443.2, C447.2, C448.2, C449.2, C450.2, C451.2, J401.2, Q401.2 (S), Q402.1 (E1), Q404.2 (S), Q405.2 (S), R405.2, R406.2, R415.1, R417.1, R421.2, R424.2, R429.2, R431.2, R437.1, R439.1, SW401.2 (C), U401.7 (PGND1), U401.8 (PGND2), U401.21 (AGND), U401.49 (PAD), U402.8 (DEF), U403.2 (GND), U404.3 (GND)
unnamed: C406.1, R401.2
unnamed: C407.1, R401.1, U401.46 (COMP1)
unnamed: C408.1, R402.2
unnamed: C409.1, R402.1, U401.15 (COMP2)
unnamed: C410.1, R403.2
unnamed: C411.1, R403.1, U401.25 (COMP3)
unnamed: C412.1, R404.2
unnamed: C413.1, R404.1, U401.36 (COMP4)
unnamed: C415.1, U401.45 (SS1_PG1)
unnamed: C416.1, U401.16 (SS2_PG2)
unnamed: C417.1, U401.24 (SS3_PG3)
unnamed: C418.1, U401.37 (SS4_PG4)
unnamed: C420.1, U401.18 (VDDG)
unnamed: C421.1, R409.2
unnamed: C424.1, R408.2
unnamed: C424.2, L403.1, L404.1, U401.29 (SW3)
unnamed: C425.1, R410.2
unnamed: C425.2, L405.1, L406.1, U401.9 (SW2), U401.10 (SW2), U401.11 (SW2)
unnamed: C426.1, R411.2
unnamed: C426.2, L407.1, L408.1, U401.32 (SW4)
unnamed: C427.2, R412.2, R413.2, U401.26 (VFB3)
unnamed: C428.2, R414.2, R415.2, U401.14 (VFB2)
unnamed: C429.2, R416.2, R417.2, U401.35 (VFB4)
unnamed: C430.2, R418.2, R420.1, U401.47 (VFB1)
unnamed: C437.2, C438.2, R420.2, R421.1
unnamed: C442.2, U402.9 (SS_TR)
unnamed: C443.1, R428.2, R429.1
unnamed: C446.2, Q406.1 (G), R432.1, R433.2
unnamed: L409.2, U402.1 (SW), U402.2 (SW), U402.3 (SW)
unnamed: LED401.1, Q401.3 (D)
unnamed: LED401.2, R422.2
unnamed: Q402.2 (B1), R425.1
unnamed: Q402.6 (C1), R426.2, R427.2
unnamed: Q403.1 (E), R428.1
unnamed: Q403.2 (B), R427.1
unnamed: Q404.3 (D), R433.1
unnamed: Q405.1 (G), R434.2, R435.2, SW401.3 (A)
unnamed: Q407.1 (E), R438.2
unnamed: Q407.2 (B), R435.1
unnamed: R405.1, U401.38 (I2CADDR)
unnamed: R406.1, U401.40 (RCLOCK_SYNC)
unnamed: R407.1, U401.39 (RST_N)
unnamed: R408.1, U401.28 (CB3)
unnamed: R409.1, U401.1 (CB1)
unnamed: R410.1, U401.12 (CB2)
unnamed: R411.1, U401.33 (CB4)
unnamed: R423.2, R424.1, U402.7 (FSW)
unnamed: R430.2, R431.1, U402.5 (FB)
unnamed: U402.6 (AGND), U402.15 (PGND), U402.16 (PGND), U402.17 (EP)
PG_ALL: C428.1, C432.1, C435.1, C439.1, L405.2, L406.2, Q401.1 (G), R414.1, R419.1, R419.2, R422.1, U401.17 (PGOOD)
SCL: U401.43 (SCL)
SDA: U401.42 (SDA)
VCC1V0: C421.2, C430.1, C437.1, C438.1, L401.1, L401.2, L402.1, L402.2, R418.1, U401.2 (SW1), U401.3 (SW1), U401.4 (SW1)
VCC1V5: C429.1, C433.1, C436.1, L407.2, L408.2, R416.1
VCC1V8: C427.1, C431.1, C434.1, C447.1, FB401.2, L403.2, L404.2, R412.1
VCC5V0: C401.1, C402.1, C403.1, C404.1, C405.1, C414.1, C419.1, C444.1, C445.1, C448.1, L409.1, R423.1, R430.1, R436.2, U401.5 (PVIN1), U401.6 (PVIN2), U401.22 (VIN), U401.30 (PVIN3), U401.31 (PVIN4), U402.14 (VOS), U403.1 (IN), U403.3 (EN)
VDDD: C422.2, C423.2, R407.2, U401.19 (VDDA), U401.20 (VDDD)
VU: C440.1, C441.1, C446.1, J401.1, Q403.3 (C), Q406.2 (S), Q407.3 (C), R426.1, R432.2, R434.1, U402.10 (AVIN), U402.11 (PVIN), U402.12 (PVIN)
VU_CK: Q406.3 (D)
XADC1V8: C449.1, FB401.1, U404.1 (IN)
XADCVREF: C451.1, U404.2 (OUT)

Notes on the sheet:
MUST CHECK THIS ONCE
