ee23btech11217/Prism/PCB/SD_USB.sch

## KiCad design PCB/SD_USB.sch (2025-03-01, last stored version)

Schematic: SD_USB.sch

Parts:
C63, C64, C74, C88: .47uF; C_0603_1608Metric; MPN GRM188R71C474KA88D
C65, C66, C83: 4.7uF; C_0603_1608Metric; MPN GRM21BR61A475KA73L
C67, C68, C78, C79: 100uF; C_1210; MPN JMK325ABJ107MM-P
C69, C80: 2.2uF; C_0402; MPN GRM155R61A225KE95D
C70, C73, C75, C76, C77, C81, C82, C84, C87: .1uF; C_0603_1608Metric; MPN GRM188R71C104KA01D
C71, C72, C85, C86: 18pF; C_0402_1005Metric
D3: BLUE LED; LED_0603; MPN VLMB1300-GS08
J6: Micro_SD_Card_Det; AMPHENOL-114-00841-68
J7: USB_A; USB-A-Receptacle-FCI_87583
J8: USB_B; USB_B_Amphenol_MUSB-D511_Vertical_Rugged
R21, R22, R23, R24, R25, R26, R27: 20k
R28, R29: 4.7k; R_0402_1005Metric; MPN RC0402FR-074K7L
R30, R34, R37: 10k; R_0402_1005Metric; MPN RC0402FR-0710KL
R31: 47
R32: 150; R_0402_1005Metric; MPN RC0402FR-07150RL
R33: 47k
R35, R38: 1M; R_0402_1005Metric
R36, R39: 8.06k 1%; R_0402_1005Metric
U5: xc7z020clg400; BGA-400_21.0x21.0mm_Layout20x20_P1.0mm
U7: S25FL256SAGNFI001
U8, U10: USB3320; 32QFN-3304-5x5B
U9: MIC2025-1YMM; Crystal_HC35-U
Y1, Y2: Crystal; Crystal_HC35-U

Notes on the sheet:
JTAG Signals
Host USB 0
Fixed Host Mode
Active High En
Device USB 1
Both Banks 3v3
PLLs Enabled, JTAG Cascade, QSPI Boot
RGMII Ref, Safe to Float
