ee23btech11217/Prism/PCB/Storage.kicad_sch

## KiCad design PCB/Storage.kicad_sch (2025-03-09, last stored version)

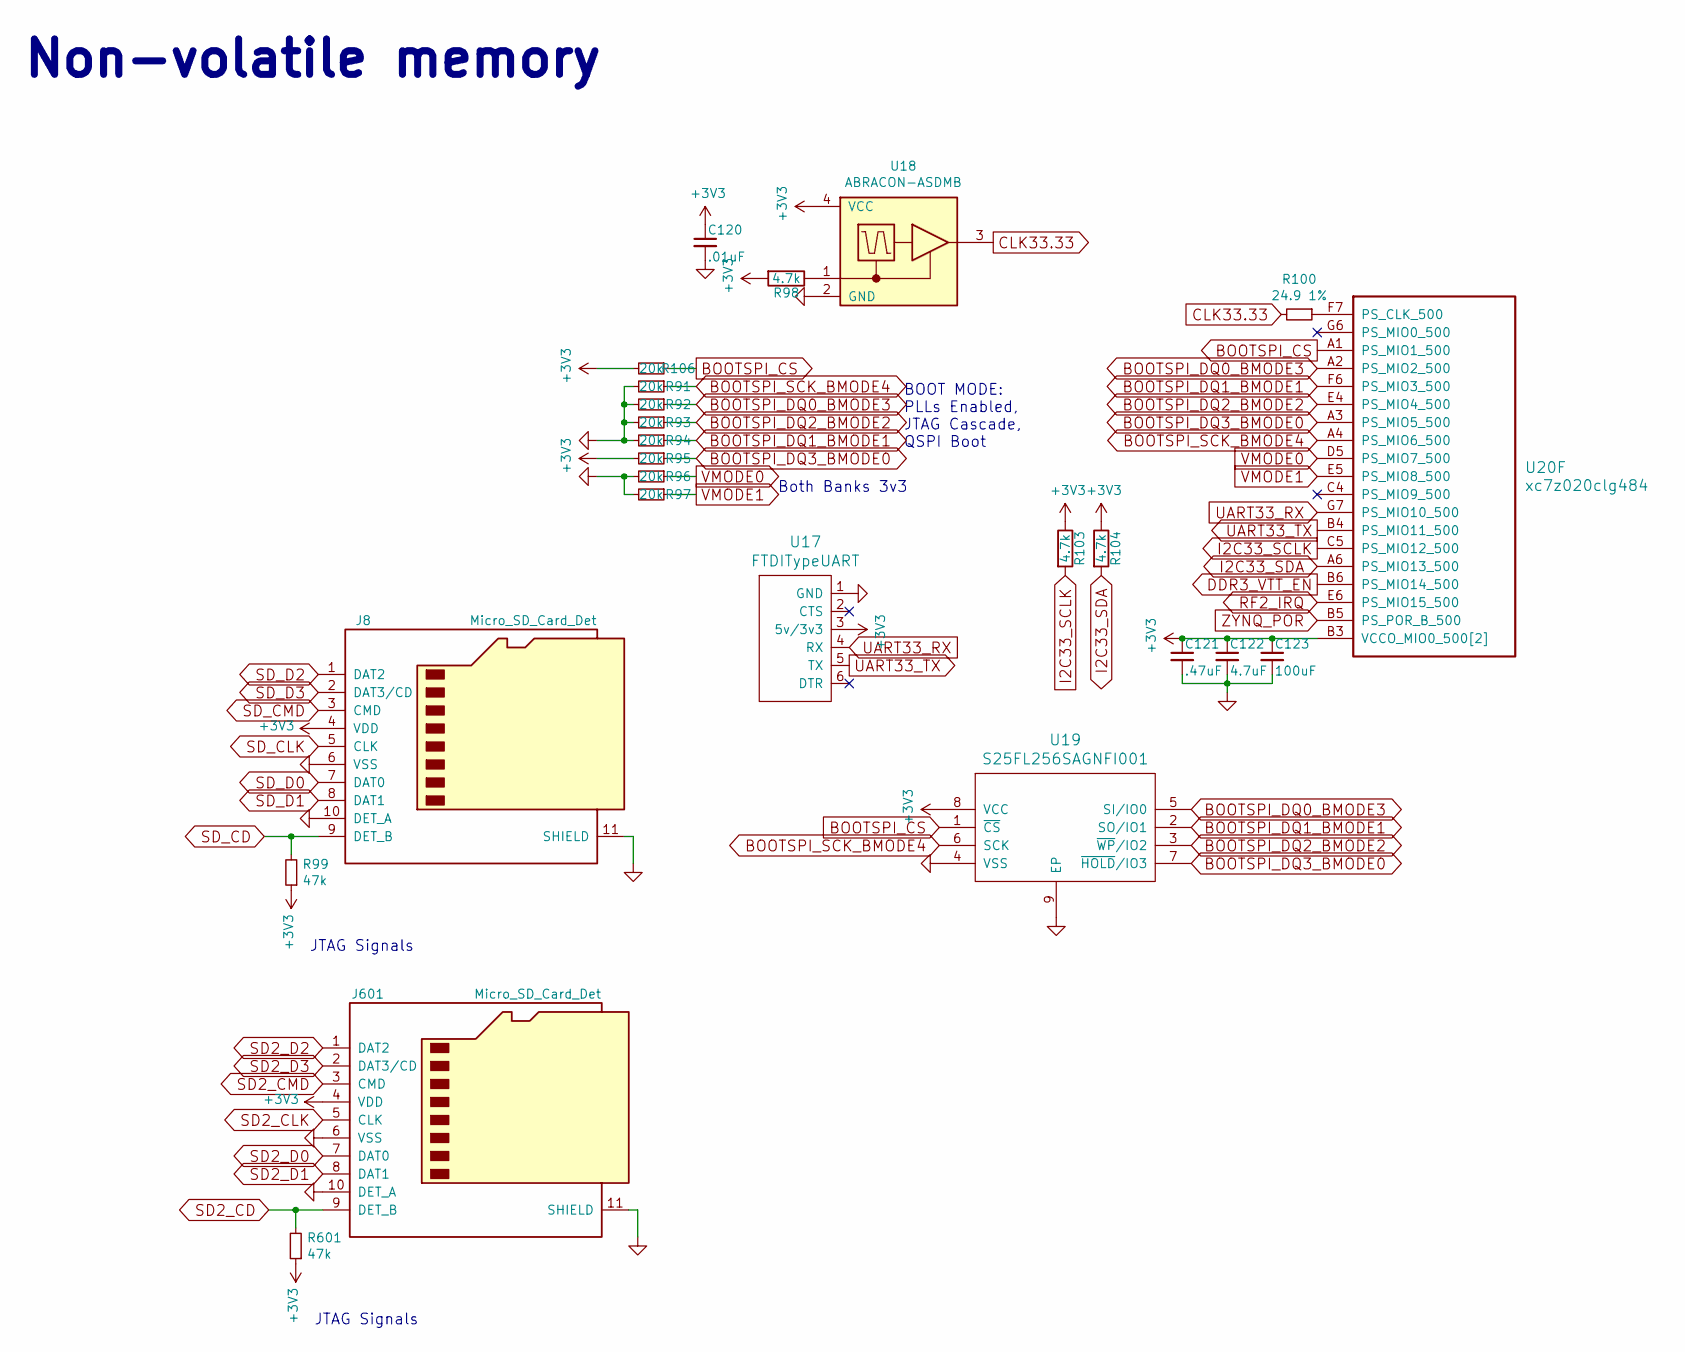
[picture p16: schematic Storage.kicad_sch]

Parts:
C120: .01uF; C_0402_1005Metric; MPN GRM155R71H103KA88J
C121: .47uF; C_0402_1005Metric; MPN CC0402KRX5R5BB474
C122: 4.7uF; C_0402_1005Metric; MPN GRM155R60G475ME47D
C123: 100uF; C_1210_3225Metric; MPN JMK325ABJ107MM-P
J8, J601: Micro_SD_Card_Det; AMPHENOL-114-00841-68; MPN 114-00841-68
R91, R92, R93, R94, R95, R96, R97, R106: 20k; R_0402_1005Metric; MPN RT0402BRD0720KL
R98, R103, R104: 4.7k; R_0402_1005Metric; MPN RC0402JR-074K7L
R99, R601: 47k; R_0402_1005Metric; MPN RC0402FR-0747KL
R100: 24.9 1%; R_0402_1005Metric; MPN RC0402FR-0724K9L
U17: FTDITypeUART; FTDI_CONN
U18: ABRACON-ASDMB; XTAL_ASDMB-24.000MHZ-LC-T; MPN ASDMB-24.000MHZ-LC-T
U19: S25FL256SAGNFI001; Cypress-002-18827-0-0-0; MPN S25FL256SAGNFI001
U20: xc7z020clg484; BGA-484_19.0x19.0mm_Layout22x22_P0.80mm_dia0.40mm

Connections:
+3V3: C120.1, C121.1, C122.1, C123.1, J8.4 (VDD), J601.4 (VDD), R95.2, R98.2, R99.1, R103.1, R104.1, R106.2, R601.1, U17.3 (5v/3v3), U18.4 (VCC), U19.8 (VCC), U20.B3 (VCCO_MIO0_500[2]), U20.C6 (VCCO_MIO0_500[2])
BOOTSPI_CS: R106.1, U19.1 (~CS), U20.A1 (PS_MIO1_500)
BOOTSPI_DQ0_BMODE3: R92.1, U19.5 (SI/IO0), U20.A2 (PS_MIO2_500)
BOOTSPI_DQ1_BMODE1: R94.1, U19.2 (SO/IO1), U20.F6 (PS_MIO3_500)
BOOTSPI_DQ2_BMODE2: R93.1, U19.3 (~WP/IO2), U20.E4 (PS_MIO4_500)
BOOTSPI_DQ3_BMODE0: R95.1, U19.7 (~HOLD/IO3), U20.A3 (PS_MIO5_500)
BOOTSPI_SCK_BMODE4: R91.1, U19.6 (SCK), U20.A4 (PS_MIO6_500)
CLK33.33: R100.2, U18.3 (OUT)
DDR3_VTT_EN: U20.B6 (PS_MIO14_500)
GND: C120.2, C121.2, C122.2, C123.2, J8.6 (VSS), J8.10 (DET_A), J8.11 (SHIELD), J601.6 (VSS), J601.10 (DET_A), J601.11 (SHIELD), R91.2, R92.2, R93.2, R94.2, R96.2, R97.2, U17.1 (GND), U18.2 (GND), U19.4 (VSS), U19.9 (EP)
I2C33_SCLK: R103.2, U20.C5 (PS_MIO12_500)
I2C33_SDA: R104.2, U20.A6 (PS_MIO13_500)
unnamed: R98.1, U18.1 (OE)
unnamed: R100.1, U20.F7 (PS_CLK_500)
RF2_IRQ: U20.E6 (PS_MIO15_500)
SD2_CD: J601.9 (DET_B), R601.2
SD2_CLK: J601.5 (CLK)
SD2_CMD: J601.3 (CMD)
SD2_D0: J601.7 (DAT0)
SD2_D1: J601.8 (DAT1)
SD2_D2: J601.1 (DAT2)
SD2_D3: J601.2 (DAT3/CD)
SD_CD: J8.9 (DET_B), R99.2
SD_CLK: J8.5 (CLK)
SD_CMD: J8.3 (CMD)
SD_D0: J8.7 (DAT0)
SD_D1: J8.8 (DAT1)
SD_D2: J8.1 (DAT2)
SD_D3: J8.2 (DAT3/CD)
UART33_RX: U17.4 (RX), U20.G7 (PS_MIO10_500)
UART33_TX: U17.5 (TX), U20.B4 (PS_MIO11_500)
VMODE0: R96.1, U20.D5 (PS_MIO7_500)
VMODE1: R97.1, U20.E5 (PS_MIO8_500)
ZYNQ_POR: U20.B5 (PS_POR_B_500)

Notes on the sheet:
JTAG Signals
Both Banks 3v3
BOOT MODE: PLLs Enabled, JTAG Cascade, QSPI Boot
Non-volatile memory
