ee23btech11217/Prism/PCB/USB.kicad_sch

## KiCad design PCB/USB.kicad_sch (2025-03-09, last stored version)

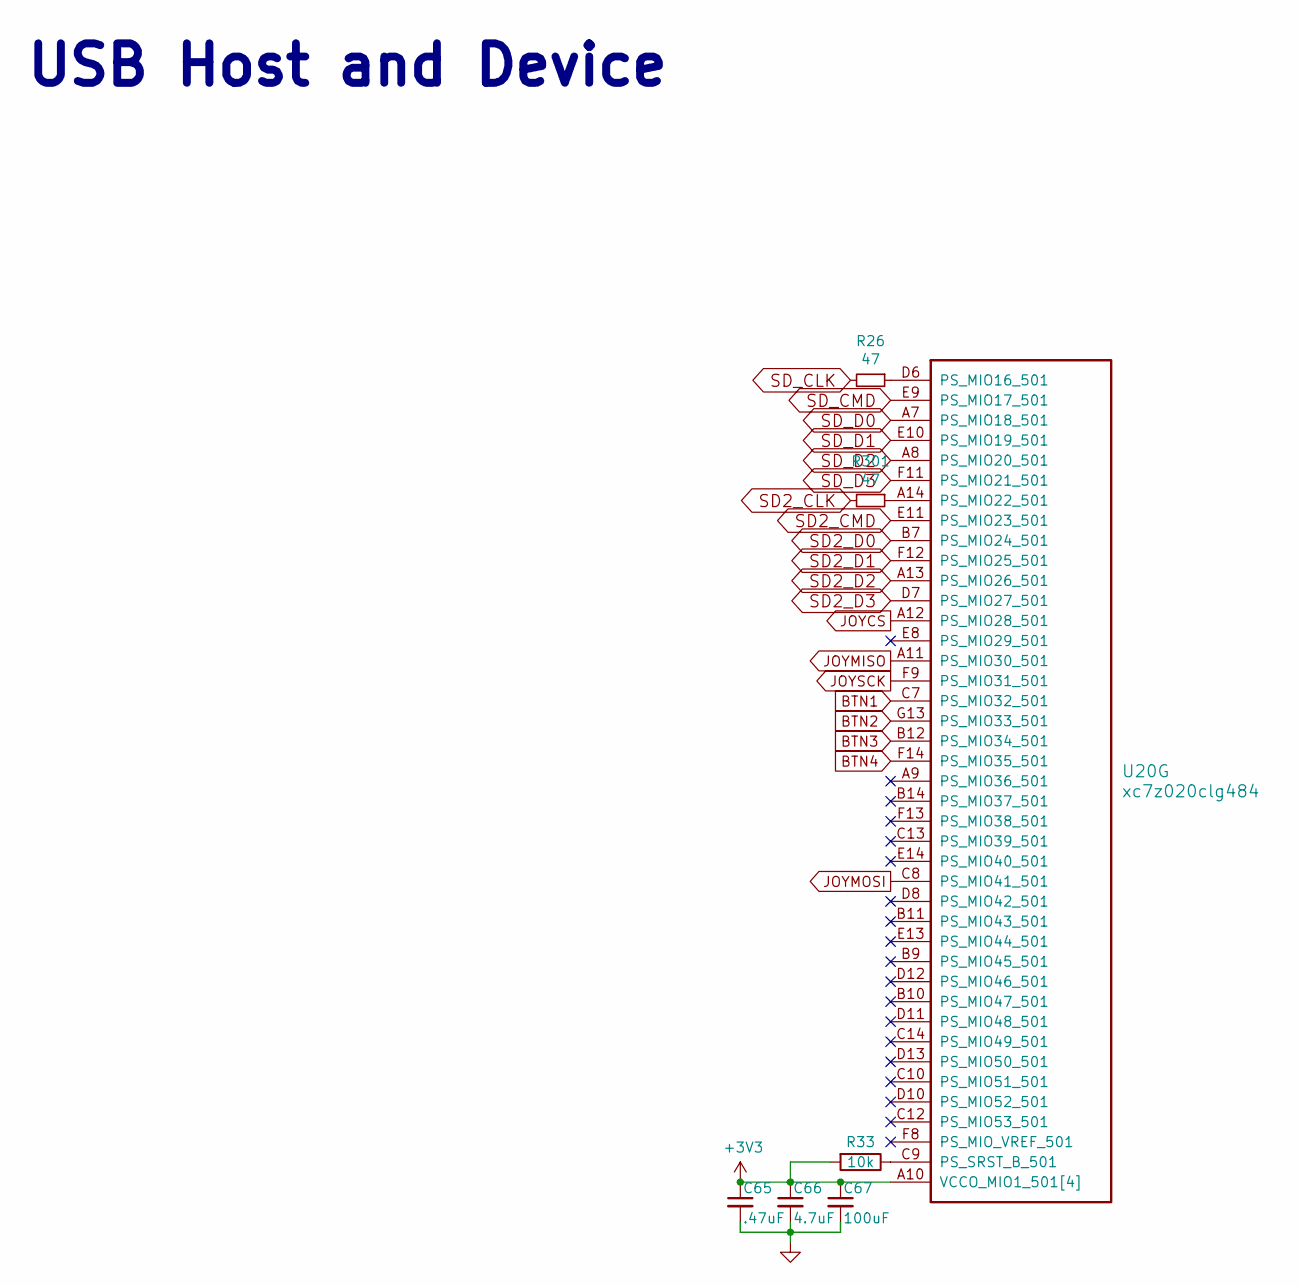
[picture p17: schematic USB.kicad_sch]

Parts:
C65: .47uF; C_0402_1005Metric; MPN CC0402KRX5R5BB474
C66: 4.7uF; C_0402_1005Metric; MPN GRM155R60G475ME47D
C67: 100uF; C_1210_3225Metric; MPN JMK325ABJ107MM-P
R26, R301: 47; R_0402_1005Metric; MPN RC0402JR-0747RL
R33: 10k; R_0402_1005Metric; MPN RC0402FR-0710KL
U20: xc7z020clg484; BGA-484_19.0x19.0mm_Layout22x22_P0.80mm_dia0.40mm

Connections:
+3V3: C65.1, C66.1, C67.1, R33.2, U20.A10 (VCCO_MIO1_501[4]), U20.B13 (VCCO_MIO1_501[4]), U20.D9 (VCCO_MIO1_501[4]), U20.E12 (VCCO_MIO1_501[4])
BTN1: U20.C7 (PS_MIO32_501)
BTN2: U20.G13 (PS_MIO33_501)
BTN3: U20.B12 (PS_MIO34_501)
BTN4: U20.F14 (PS_MIO35_501)
GND: C65.2, C66.2, C67.2
JOYCS: U20.A12 (PS_MIO28_501)
JOYMISO: U20.A11 (PS_MIO30_501)
JOYMOSI: U20.C8 (PS_MIO41_501)
JOYSCK: U20.F9 (PS_MIO31_501)
unnamed: R26.1, U20.D6 (PS_MIO16_501)
unnamed: R33.1, U20.C9 (PS_SRST_B_501)
unnamed: R301.1, U20.A14 (PS_MIO22_501)
SD2_CLK: R301.2
SD2_CMD: U20.E11 (PS_MIO23_501)
SD2_D0: U20.B7 (PS_MIO24_501)
SD2_D1: U20.F12 (PS_MIO25_501)
SD2_D2: U20.A13 (PS_MIO26_501)
SD2_D3: U20.D7 (PS_MIO27_501)
SD_CLK: R26.2
SD_CMD: U20.E9 (PS_MIO17_501)
SD_D0: U20.A7 (PS_MIO18_501)
SD_D1: U20.E10 (PS_MIO19_501)
SD_D2: U20.A8 (PS_MIO20_501)
SD_D3: U20.F11 (PS_MIO21_501)

Notes on the sheet:
USB Host and Device
