ee23btech11217/Prism/PCB/fpga-power.kicad_sch

## KiCad design PCB/fpga-power.kicad_sch (2025-03-09, last stored version)

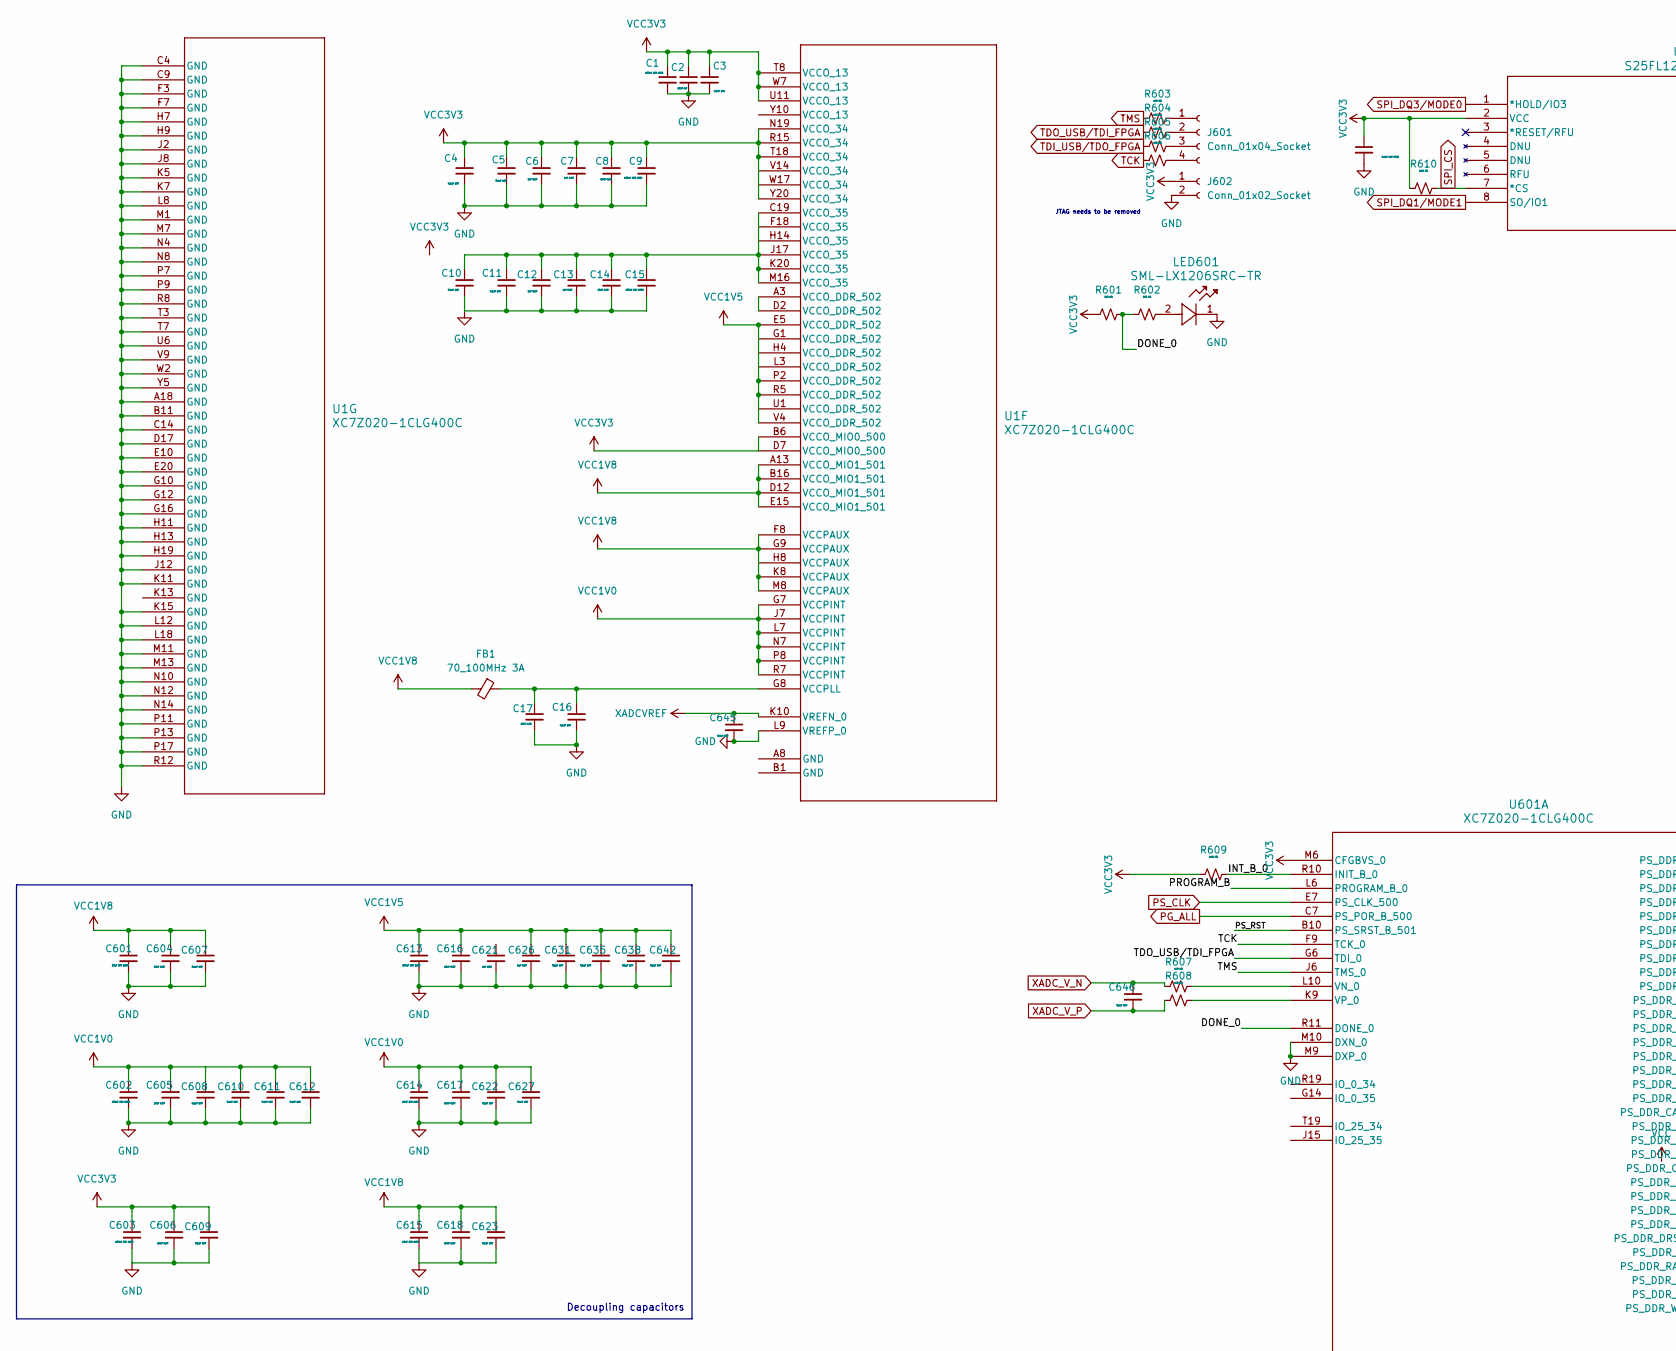
[picture p18: schematic fpga-power.kicad_sch, part in row 1, column 1]

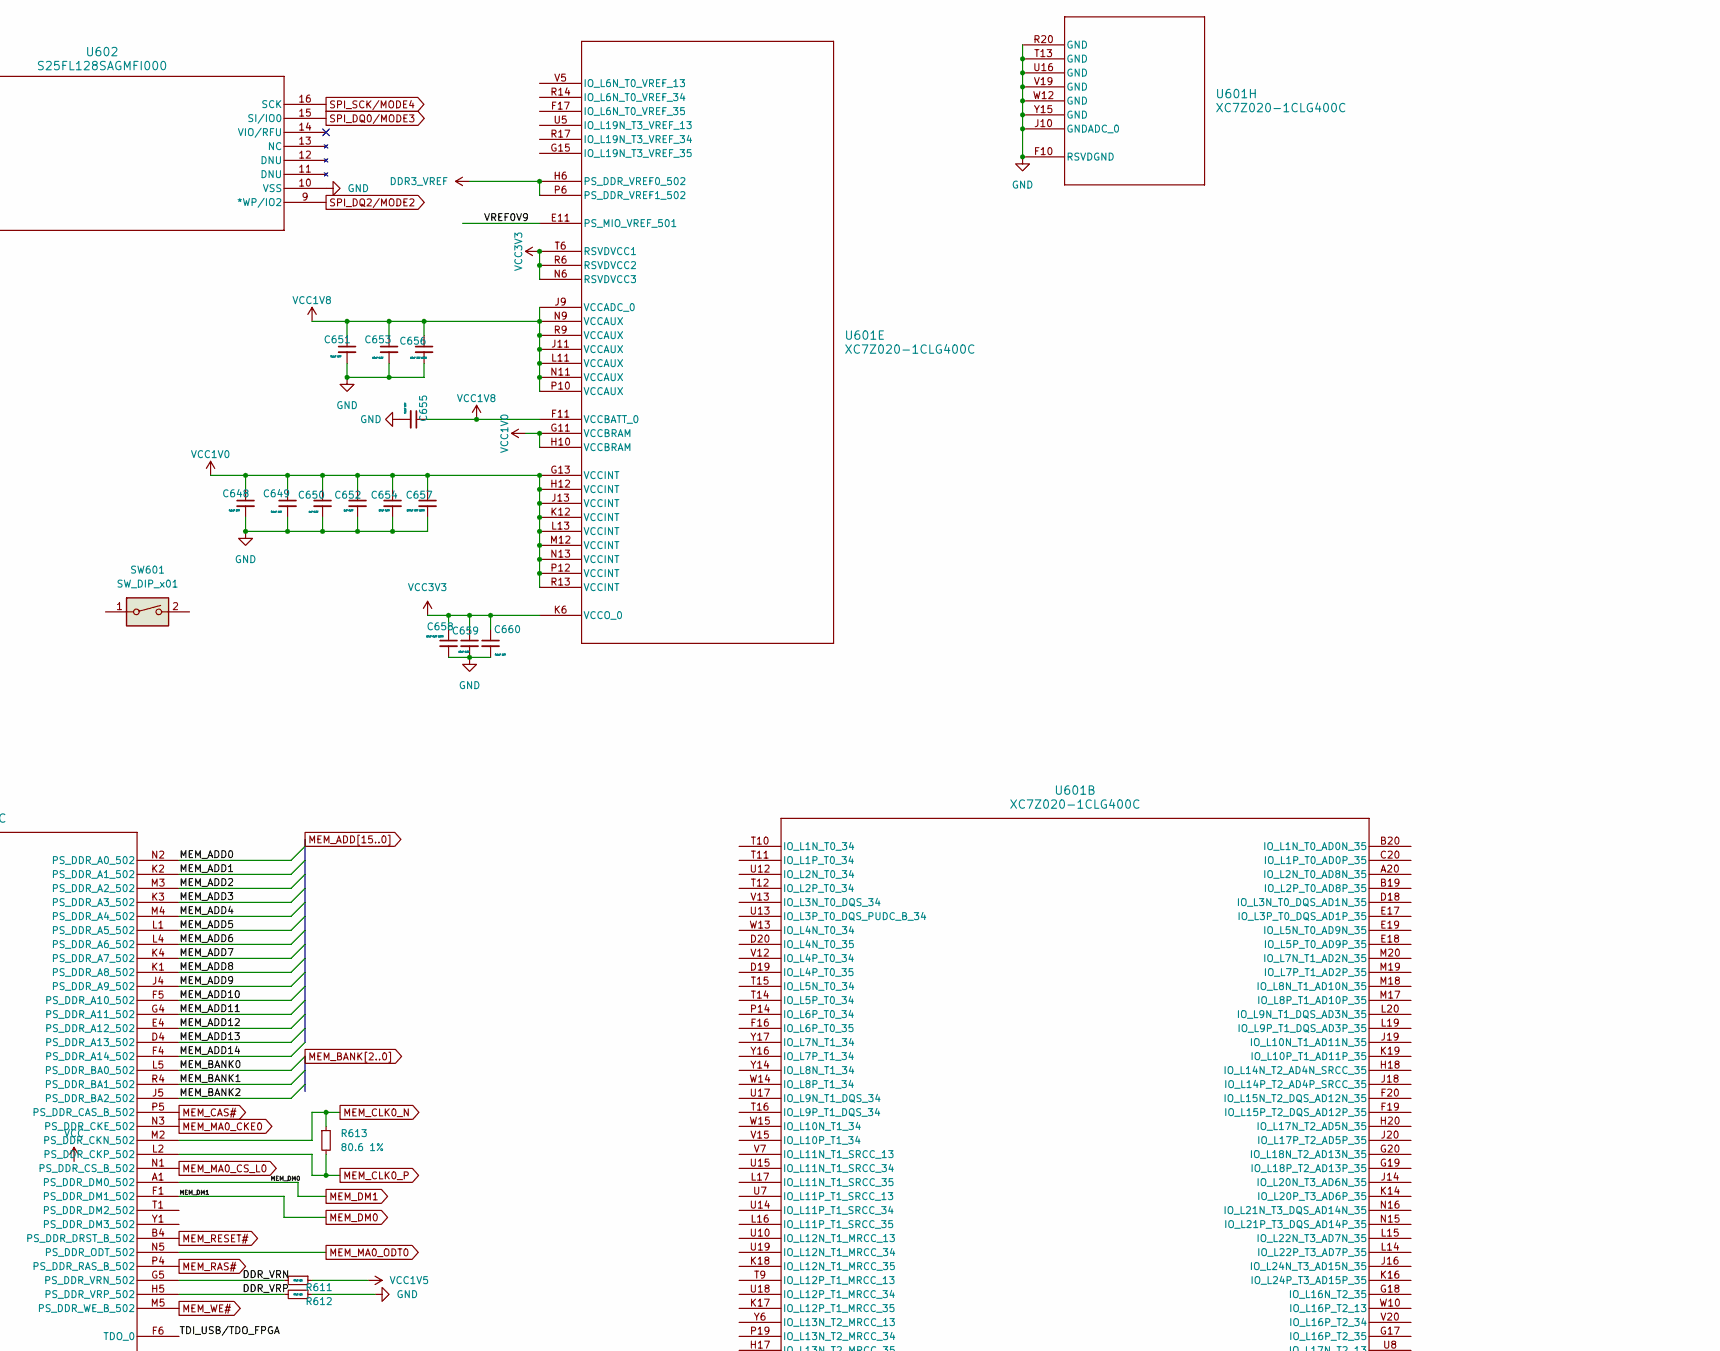
[picture p19: schematic fpga-power.kicad_sch, part in row 1, column 2]

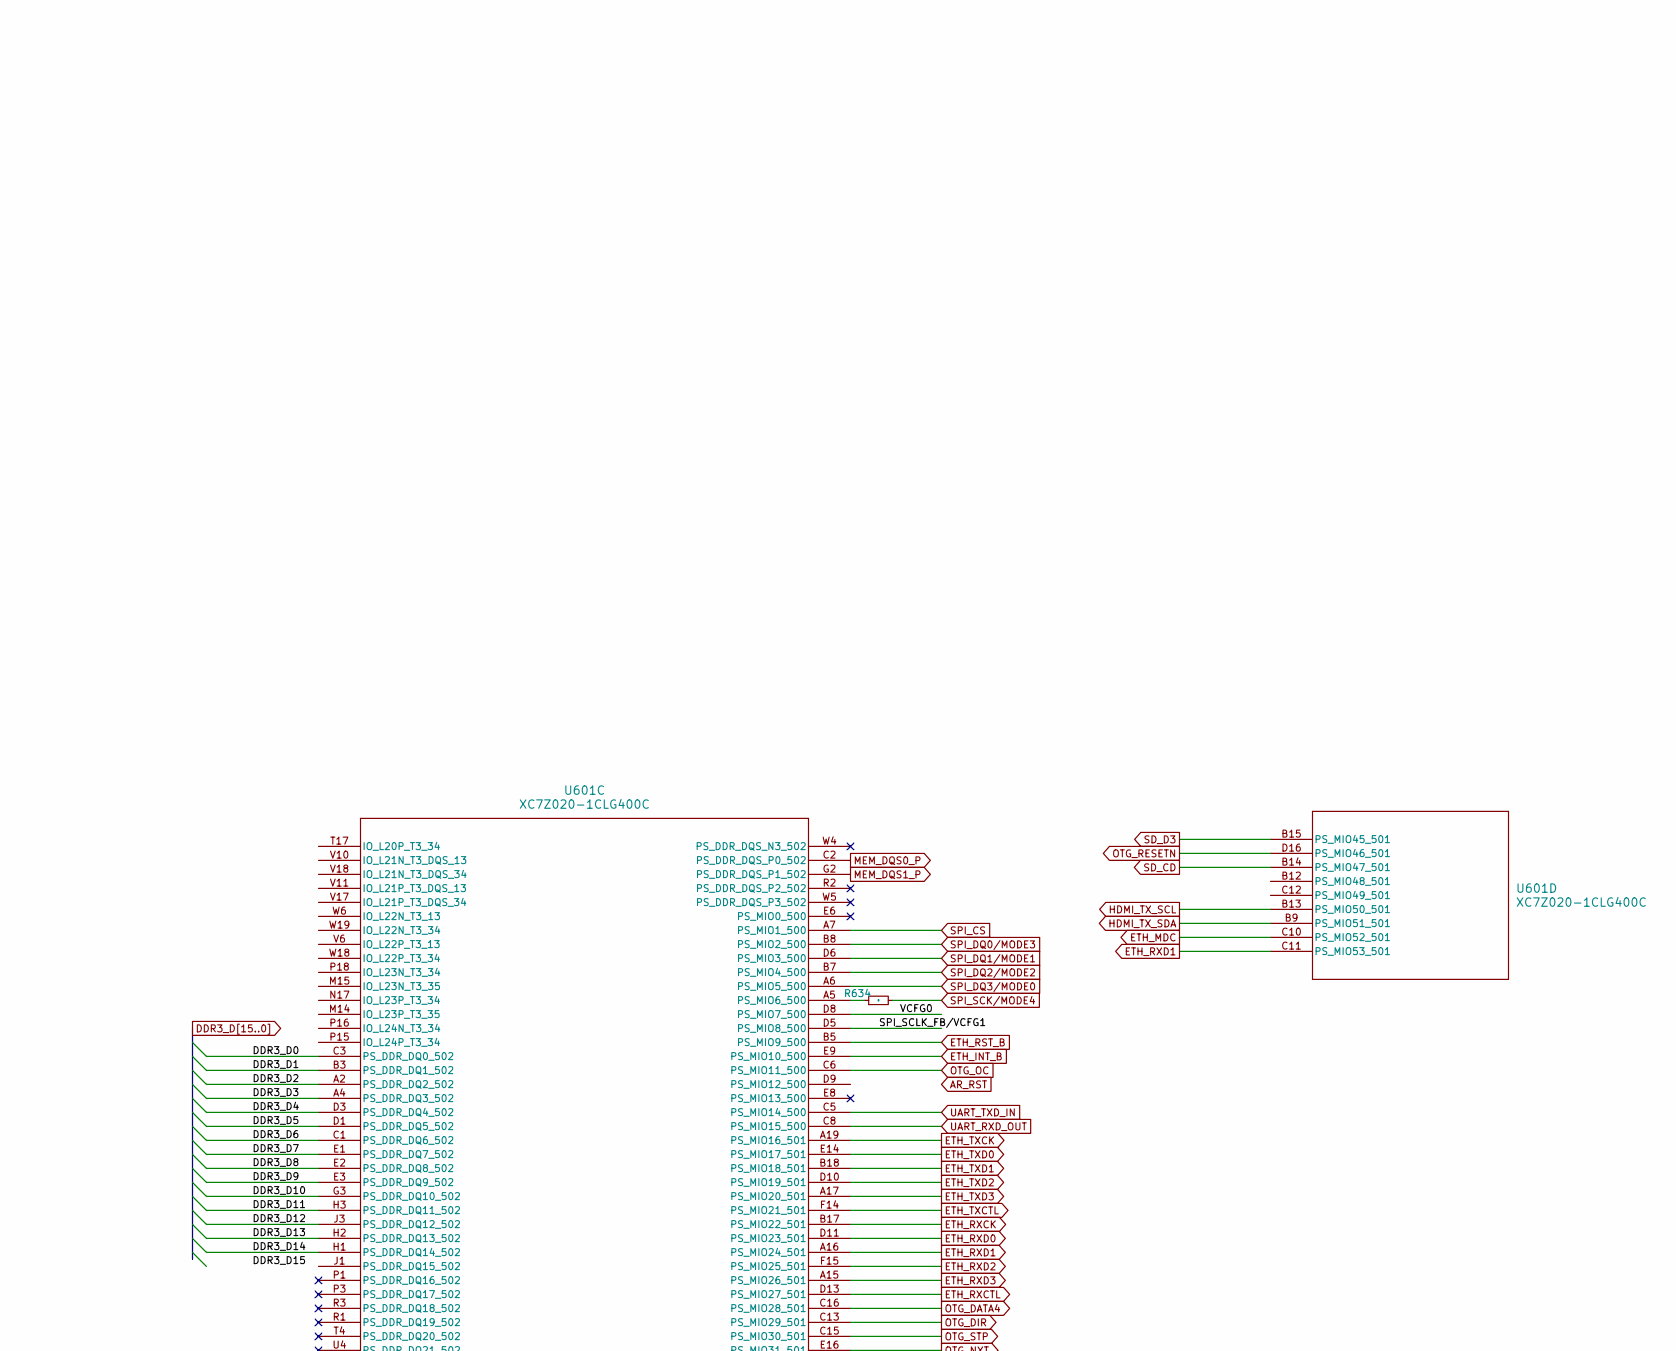
[picture p20: schematic fpga-power.kicad_sch, part in row 1, column 3]

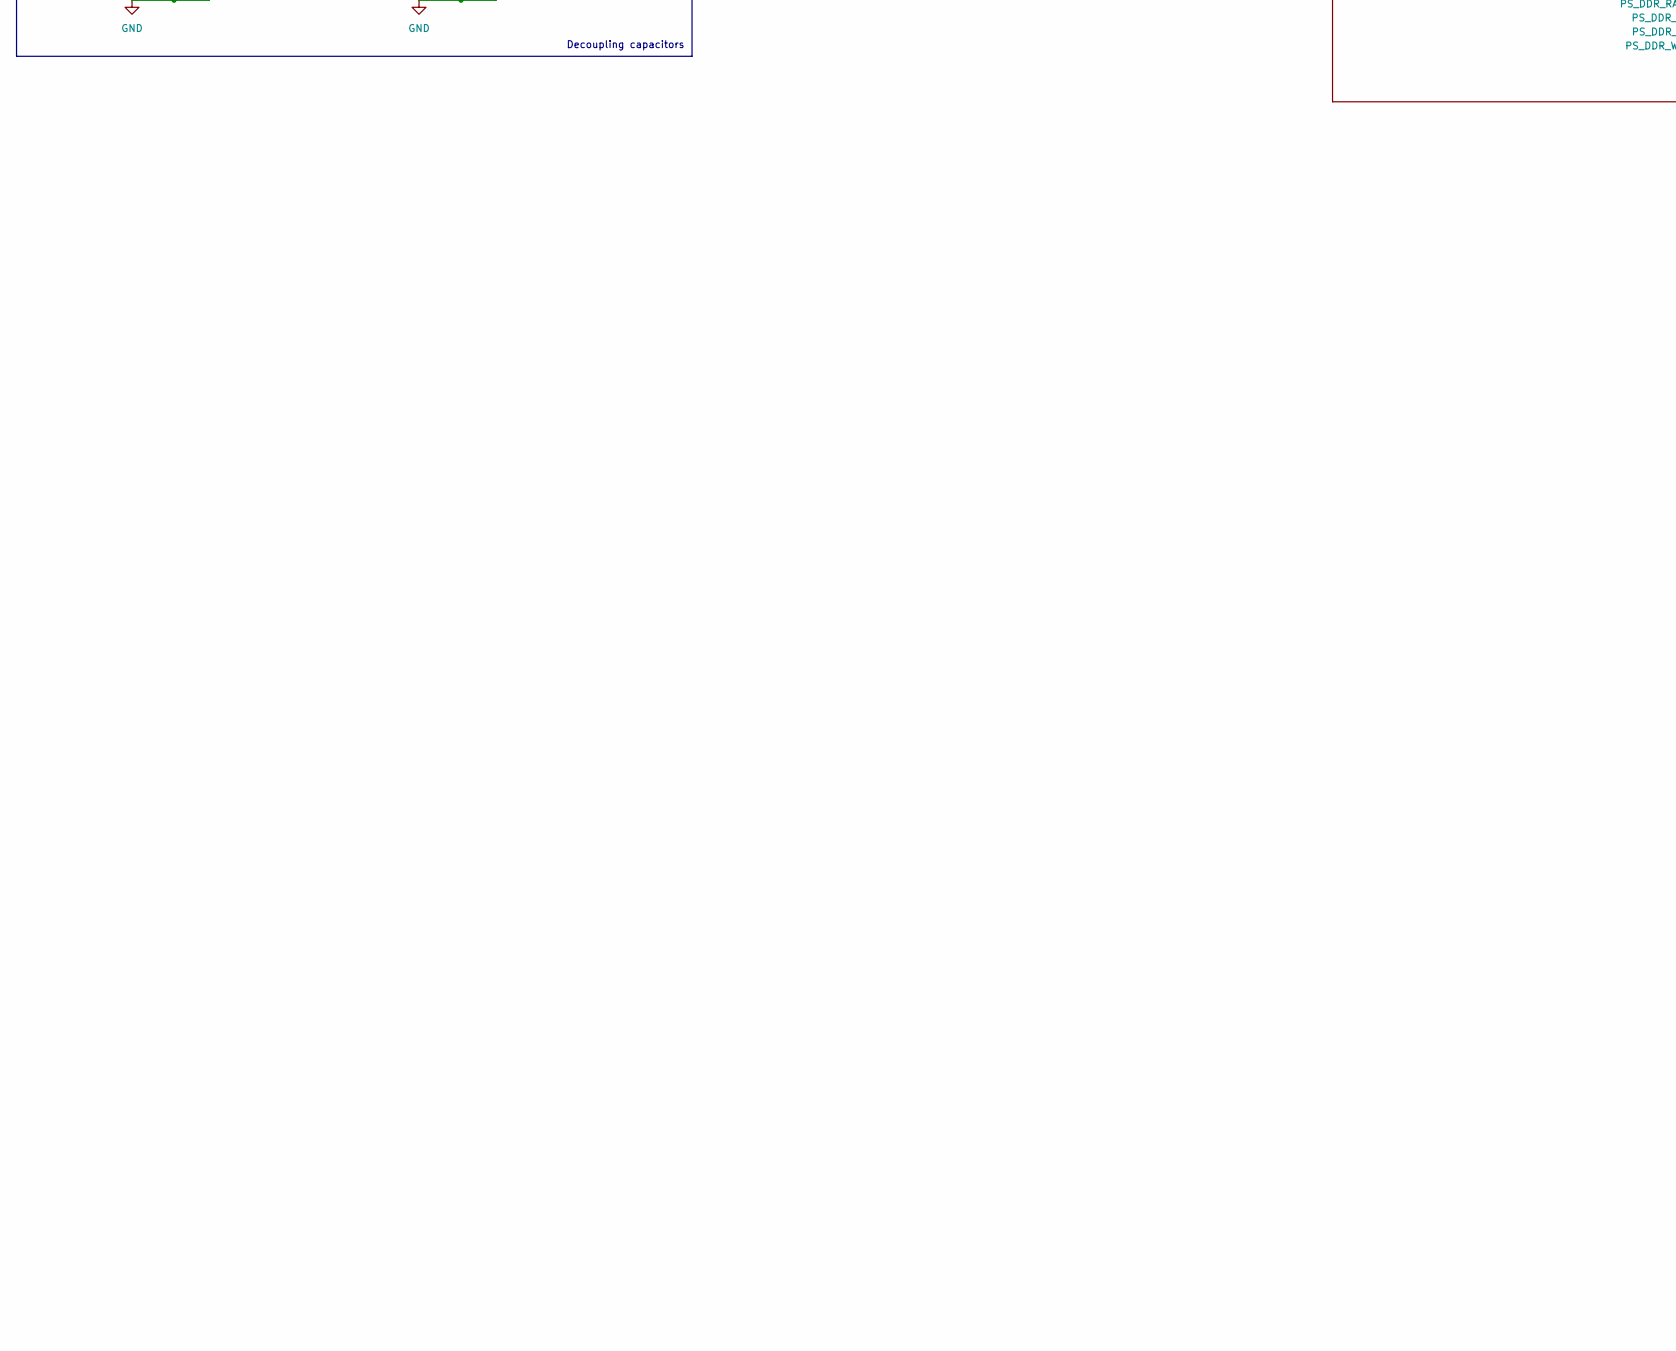
[picture p21: schematic fpga-power.kicad_sch, part in row 2, column 1]

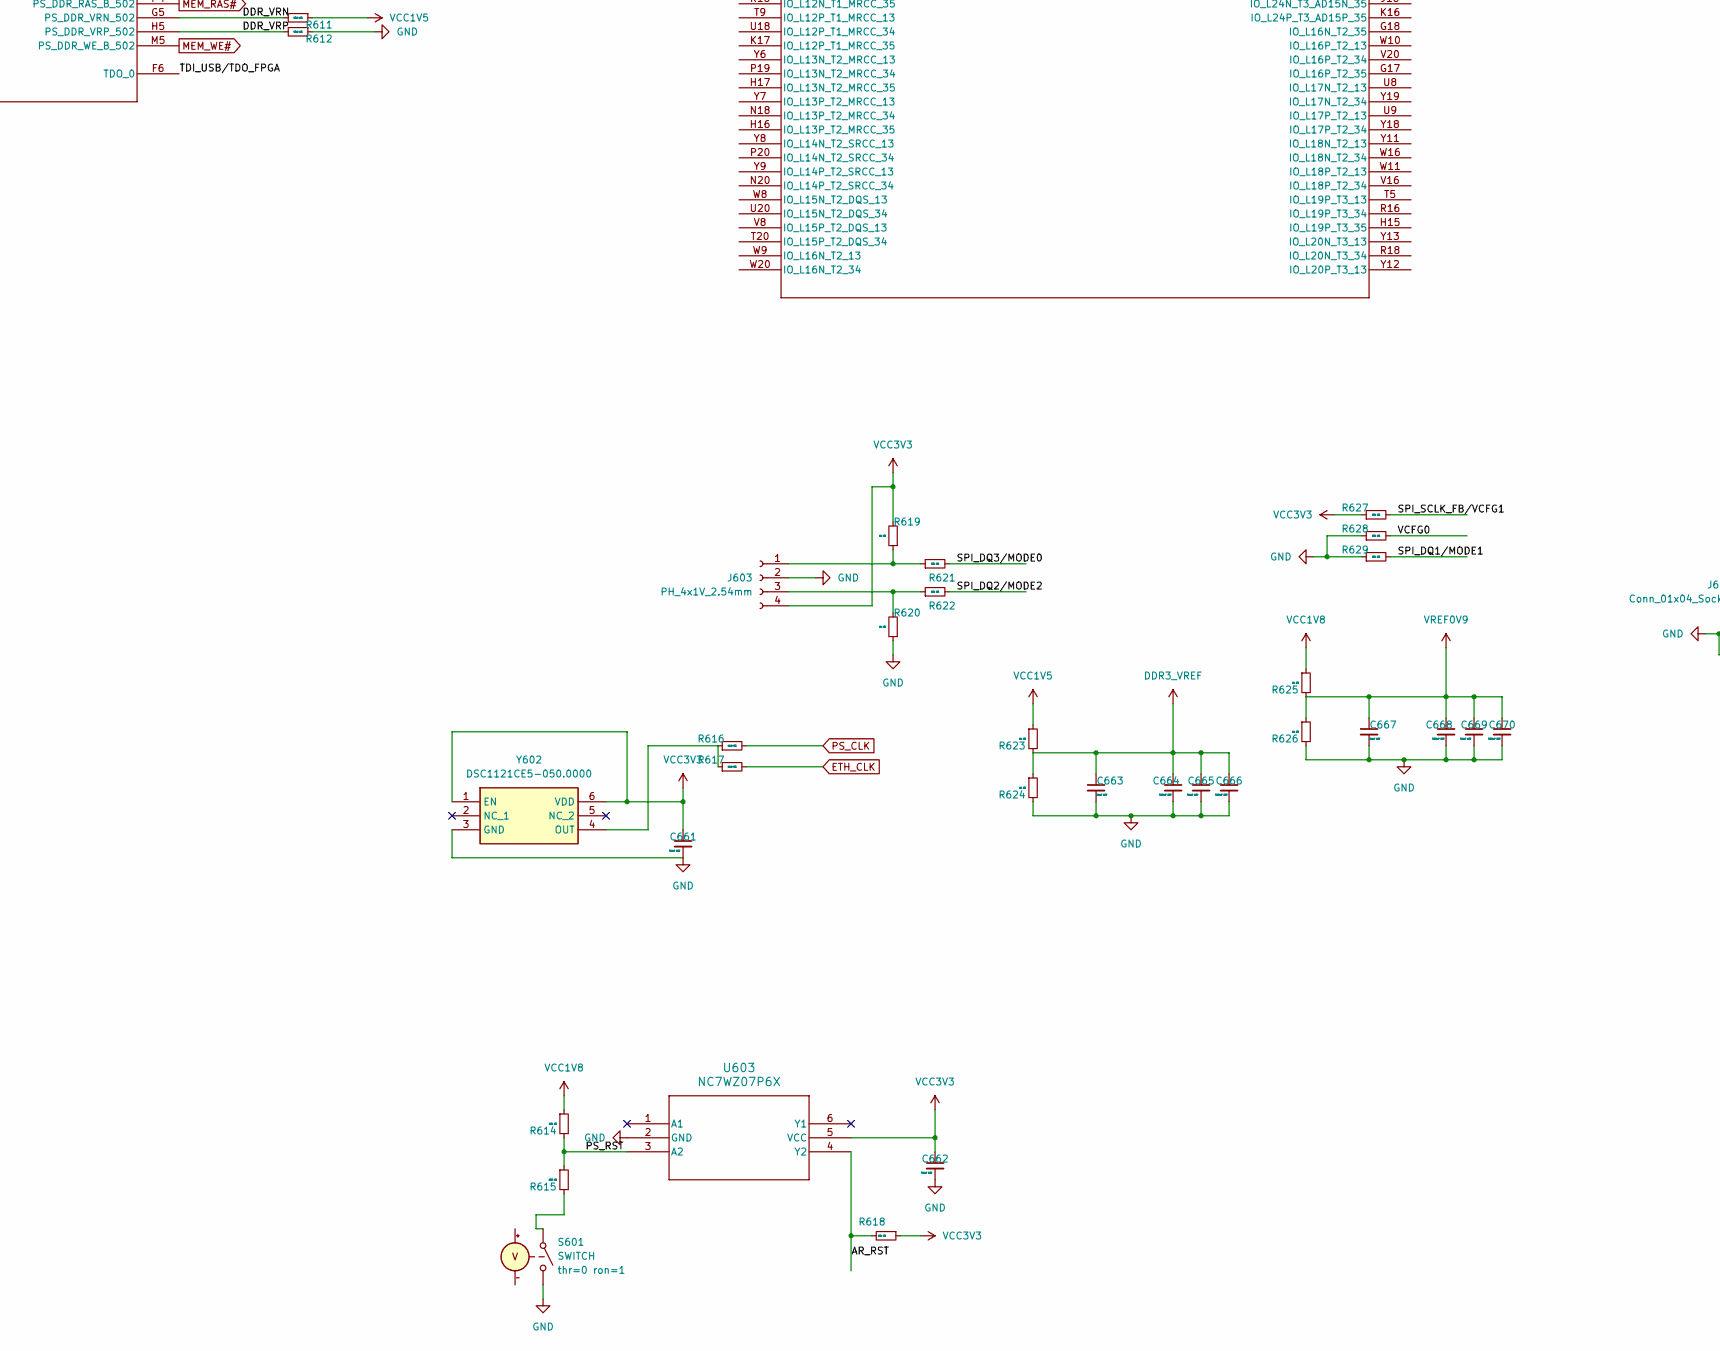
[picture p22: schematic fpga-power.kicad_sch, part in row 2, column 2]

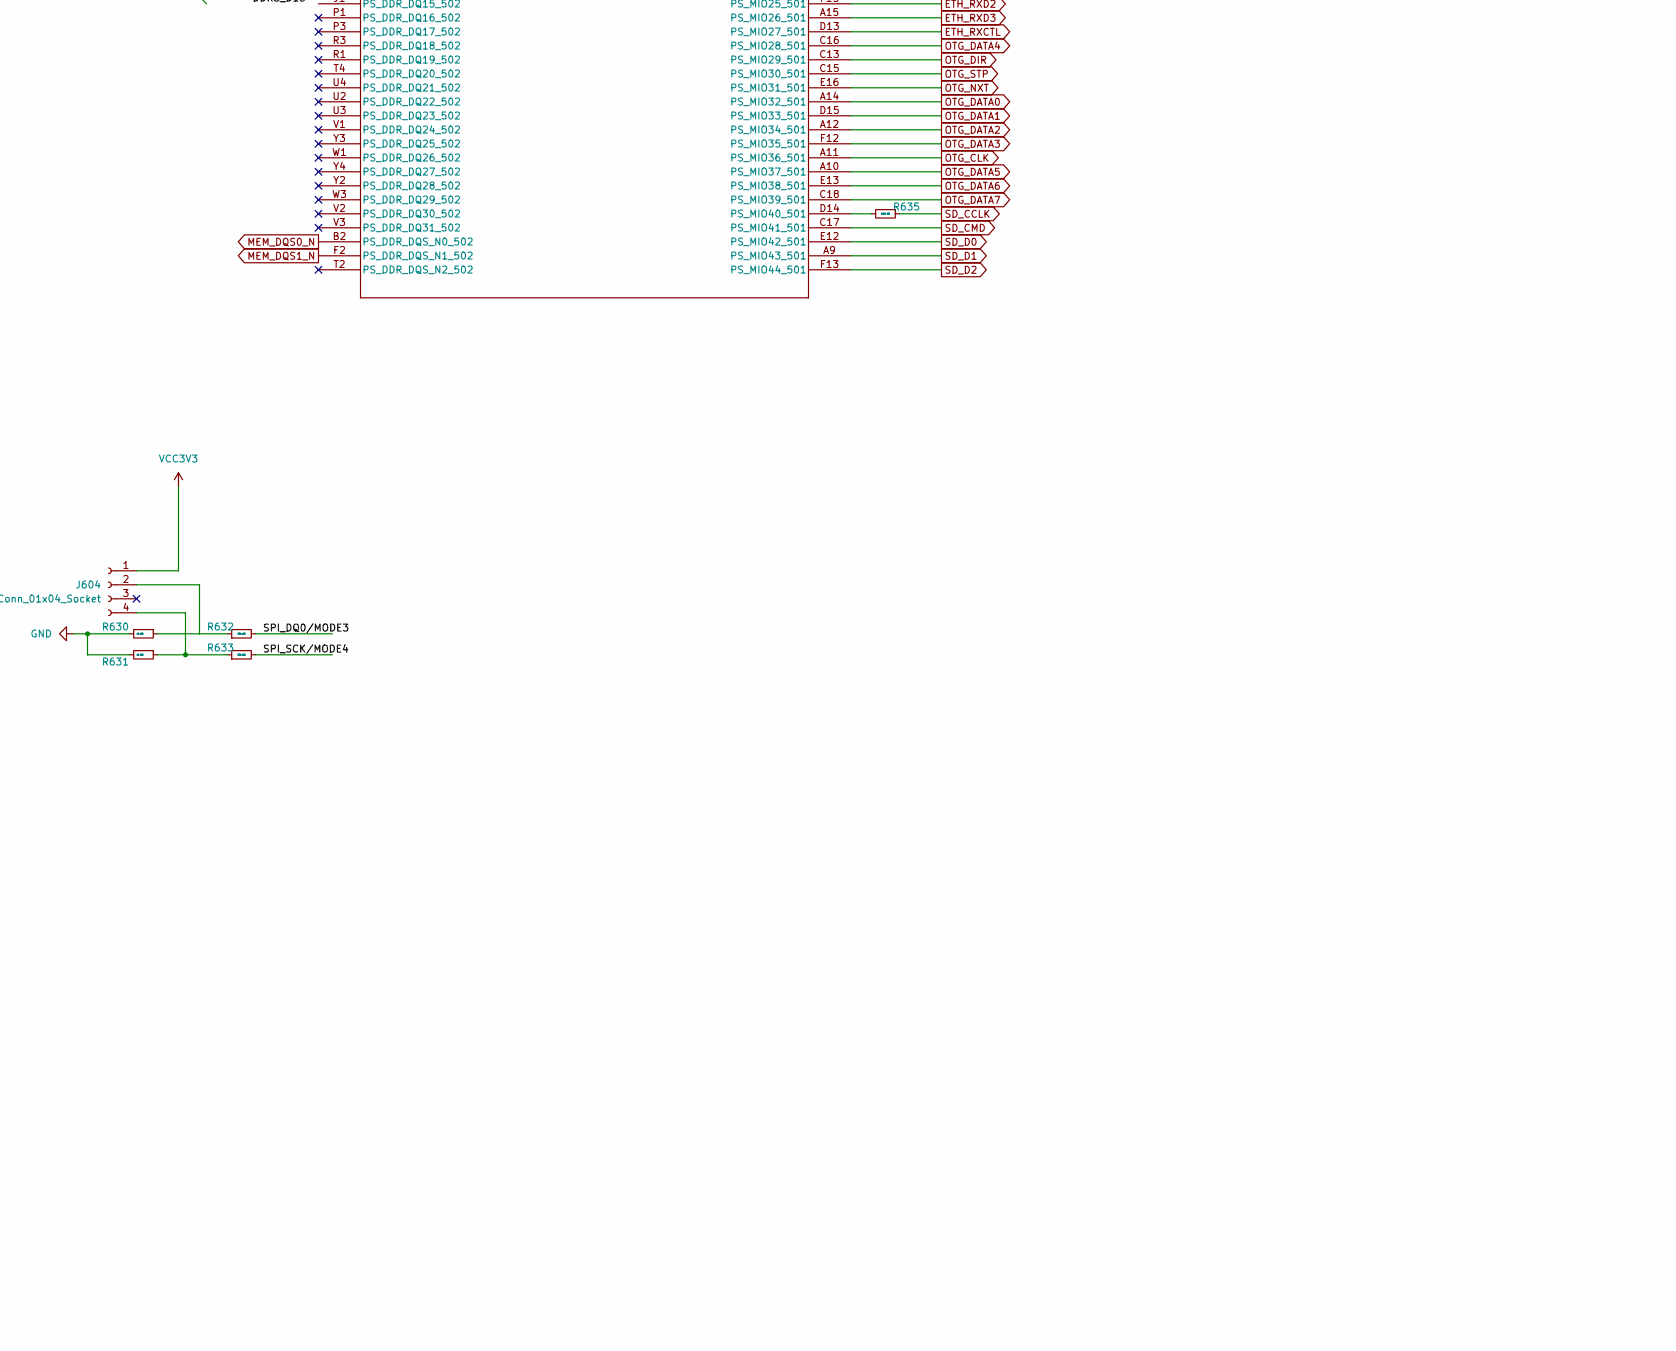
[picture p23: schematic fpga-power.kicad_sch, part in row 2, column 3]

Parts:
C1, C9, C15, C602, C603, C613, C657: 100uF 25V 1206; C_1206_3216Metric
C2: 10uF 6.V; C_0805_2012Metric
C3, C4, C5, C10, C11, C16, C607, C608, C609, C610, C611, C612, C622, C623, C627, C631, C635, C638, C642, C645, C646, C648, C649, C651, C655, C660, C661, C662, C663, C665, C667, C669: 0.1uF 16V; C_0805_2012Metric
C6, C7, C12, C13, C621, C626, C650, C652: 1uF 6.3V; C_0805_2012Metric
C8, C14, C17, C604, C605, C606, C616, C617, C618, C653, C654, C659: 10uF 6.3V; C_0805_2012Metric
C601, C614, C615, C656: 10uF 25V 1206; C_1206_3216Metric
C647: 0.1uF 16V 0805; C_0805_2012Metric
C658: 10uF 6.3V 1206; C_1206_3216Metric
C664, C666, C668, C670: 0.01uF 25V; C_0805_2012Metric
FB1: 70_100MHz 3A; L_0603_1608Metric
J601, J604: Conn_01x04_Socket
J602: Conn_01x02_Socket
J603: PH_4x1V_2.54mm
LED601: SML-LX1206SRC-TR; LED_3P2X1P5_LUM
R601, R602: 220 1%; R_0805_2012Metric
R603, R604, R605, R606: 100 5%; R_0805_2012Metric
R607, R608: 140 1%; R_0805_2012Metric
R609, R610: 4.7K 5%; R_0805_2012Metric
R611, R612, R613: 80.6 1%; R_0805_2012Metric
R614, R618: 10k 1%; R_0805_2012Metric
R615: 200 1%; R_0805_2012Metric
R616, R617: 49.9 5%; R_0805_2012Metric
R619, R620, R623, R624, R625, R626, R630, R631: 1k 1%; R_0805_2012Metric
R621, R622, R627, R628, R629, R632, R633: 20k 1%; R_0805_2012Metric
R634: 0; R_0805_2012Metric
R635: 40.2 5%; R_0805_2012Metric
S601: SWITCH
SW601: SW_DIP_x01
U1, U601: XC7Z020-1CLG400C; CLG400_ZYNQ-7000_XIL
U602: S25FL128SAGMFI000; SO3016_SPA
U603: NC7WZ07P6X; SC-88/SC70-6/SOT-363_419B-02_ONS
Y602: DSC1121CE5-050.0000; DSC1121CE50500000; Mouser Part Number 998-1121CE5-050.0000

Connections:
AR_RST: R618.2, U603.4 (Y2)
DDR3_D0: U601.C3 (PS_DDR_DQ0_502)
DDR3_D1: U601.B3 (PS_DDR_DQ1_502)
DDR3_D2: U601.A2 (PS_DDR_DQ2_502)
DDR3_D3: U601.A4 (PS_DDR_DQ3_502)
DDR3_D4: U601.D3 (PS_DDR_DQ4_502)
DDR3_D5: U601.D1 (PS_DDR_DQ5_502)
DDR3_D6: U601.C1 (PS_DDR_DQ6_502)
DDR3_D7: U601.E1 (PS_DDR_DQ7_502)
DDR3_D8: U601.E2 (PS_DDR_DQ8_502)
DDR3_D9: U601.E3 (PS_DDR_DQ9_502)
DDR3_D10: U601.G3 (PS_DDR_DQ10_502)
DDR3_D11: U601.H3 (PS_DDR_DQ11_502)
DDR3_D12: U601.J3 (PS_DDR_DQ12_502)
DDR3_D13: U601.H2 (PS_DDR_DQ13_502)
DDR3_D14: U601.H1 (PS_DDR_DQ14_502)
DDR3_VREF: C663.1, C664.1, C665.1, C666.1, R623.2, R624.1, U601.H6 (PS_DDR_VREF0_502), U601.P6 (PS_DDR_VREF1_502)
DDR_VRN: R611.2, U601.G5 (PS_DDR_VRN_502)
DDR_VRP: R612.2, U601.H5 (PS_DDR_VRP_502)
DONE_0: R601.1, R602.2, U601.R11 (DONE_0)
ETH_CLK: R617.2
ETH_INT_B: U601.E9 (PS_MIO10_500)
ETH_MDC: U601.C10 (PS_MIO52_501)
ETH_RST_B: U601.B5 (PS_MIO9_500)
ETH_RXCK: U601.B17 (PS_MIO22_501)
ETH_RXCTL: U601.D13 (PS_MIO27_501)
ETH_RXD0: U601.D11 (PS_MIO23_501)
ETH_RXD1: U601.A16 (PS_MIO24_501), U601.C11 (PS_MIO53_501)
ETH_RXD2: U601.F15 (PS_MIO25_501)
ETH_RXD3: U601.A15 (PS_MIO26_501)
ETH_TXCK: U601.A19 (PS_MIO16_501)
ETH_TXCTL: U601.F14 (PS_MIO21_501)
ETH_TXD0: U601.E14 (PS_MIO17_501)
ETH_TXD1: U601.B18 (PS_MIO18_501)
ETH_TXD2: U601.D10 (PS_MIO19_501)
ETH_TXD3: U601.A17 (PS_MIO20_501)
GND: C1.2, C2.2, C3.2, C4.2, C5.2, C6.2, C7.2, C8.2, C9.2, C10.2, C11.2, C12.2, C13.2, C14.2, C15.2, C16.2, C17.2, C601.2, C602.2, C603.2, C604.2, C605.2, C606.2, C607.2, C608.2, C609.2, C610.2, C611.2, C612.2, C613.2, C614.2, C615.2, C616.2, C617.2, C618.2, C621.2, C622.2, C623.2, C626.2, C627.2, C631.2, C635.2, C638.2, C642.2, C645.2, C647.2, C648.2, C649.2, C650.2, C651.2, C652.2, C653.2, C654.2, C655.2, C656.2, C657.2, C658.2, C659.2, C660.2, C661.2, C662.2, C663.2, C664.2, C665.2, C666.2, C667.2, C668.2, C669.2, C670.2, J602.2, J603.2, LED601.1, R612.1, R620.1, R624.2, R626.2, R628.1, R629.1, R630.2, R631.2, S601.2 (N-), U1.A18 (GND), U1.B11 (GND), U1.C4 (GND), U1.C9 (GND), U1.C14 (GND), U1.D17 (GND), U1.E10 (GND), U1.E20 (GND), U1.F3 (GND), U1.F7 (GND), U1.G10 (GND), U1.G12 (GND), U1.G16 (GND), U1.H7 (GND), U1.H9 (GND), U1.H11 (GND), U1.H13 (GND), U1.H19 (GND), U1.J2 (GND), U1.J8 (GND), U1.J12 (GND), U1.K5 (GND), U1.K7 (GND), U1.K11 (GND), U1.K15 (GND), U1.L8 (GND), U1.L9 (VREFP_0), U1.L12 (GND), U1.L18 (GND), U1.M1 (GND), U1.M7 (GND), U1.M11 (GND), U1.M13 (GND), U1.N4 (GND), U1.N8 (GND), U1.N10 (GND), U1.N12 (GND), U1.N14 (GND), U1.P7 (GND), U1.P9 (GND), U1.P11 (GND), U1.P13 (GND), U1.P17 (GND), U1.R8 (GND), U1.R12 (GND), U1.T3 (GND), U1.T7 (GND), U1.U6 (GND), U1.V9 (GND), U1.W2 (GND), U1.Y5 (GND), U601.F10 (RSVDGND), U601.J10 (GNDADC_0), U601.M9 (DXP_0), U601.M10 (DXN_0), U601.R20 (GND), U601.T13 (GND), U601.U16 (GND), U601.V19 (GND), U601.W12 (GND), U601.Y15 (GND), U602.10 (VSS), U603.2 (GND), Y602.3 (GND)
HDMI_TX_SCL: U601.B13 (PS_MIO50_501)
HDMI_TX_SDA: U601.B9 (PS_MIO51_501)
INT_B_0: R609.1, U601.R10 (INIT_B_0)
MEM_ADD0: U601.N2 (PS_DDR_A0_502)
MEM_ADD1: U601.K2 (PS_DDR_A1_502)
MEM_ADD2: U601.M3 (PS_DDR_A2_502)
MEM_ADD3: U601.K3 (PS_DDR_A3_502)
MEM_ADD4: U601.M4 (PS_DDR_A4_502)
MEM_ADD5: U601.L1 (PS_DDR_A5_502)
MEM_ADD6: U601.L4 (PS_DDR_A6_502)
MEM_ADD7: U601.K4 (PS_DDR_A7_502)
MEM_ADD8: U601.K1 (PS_DDR_A8_502)
MEM_ADD9: U601.J4 (PS_DDR_A9_502)
MEM_ADD10: U601.F5 (PS_DDR_A10_502)
MEM_ADD11: U601.G4 (PS_DDR_A11_502)
MEM_ADD12: U601.E4 (PS_DDR_A12_502)
MEM_ADD13: U601.D4 (PS_DDR_A13_502)
MEM_ADD14: U601.F4 (PS_DDR_A14_502)
MEM_BANK0: U601.L5 (PS_DDR_BA0_502)
MEM_BANK1: U601.R4 (PS_DDR_BA1_502)
MEM_BANK2: U601.J5 (PS_DDR_BA2_502)
MEM_CAS#: U601.P5 (PS_DDR_CAS_B_502)
MEM_CLK0_N: R613.1, U601.M2 (PS_DDR_CKN_502)
MEM_CLK0_P: R613.2, U601.L2 (PS_DDR_CKP_502)
MEM_DM0: U601.F1 (PS_DDR_DM1_502)
MEM_DM1: U601.A1 (PS_DDR_DM0_502)
MEM_DQS0_N: U601.B2 (PS_DDR_DQS_N0_502)
MEM_DQS0_P: U601.C2 (PS_DDR_DQS_P0_502)
MEM_DQS1_N: U601.F2 (PS_DDR_DQS_N1_502)
MEM_DQS1_P: U601.G2 (PS_DDR_DQS_P1_502)
MEM_MA0_CKE0: U601.N3 (PS_DDR_CKE_502)
MEM_MA0_CS_L0: U601.N1 (PS_DDR_CS_B_502)
MEM_MA0_ODT0: U601.N5 (PS_DDR_ODT_502)
MEM_RAS#: U601.P4 (PS_DDR_RAS_B_502)
MEM_RESET#: U601.B4 (PS_DDR_DRST_B_502)
MEM_WE#: U601.M5 (PS_DDR_WE_B_502)
unnamed: C10.1, C11.1, C12.1, C13.1, C14.1, C15.1, U1.C19 (VCCO_35), U1.J17 (VCCO_35), U1.K20 (VCCO_35), U1.M16 (VCCO_35)
unnamed: C16.1, C17.1, FB1.1, U1.G8 (VCCPLL)
unnamed: J601.1, R603.1
unnamed: J601.2, R604.1
unnamed: J601.3, R605.1
unnamed: J601.4, R606.1
unnamed: J603.1, R619.1, R621.1
unnamed: J603.3, R620.2, R622.1
unnamed: J604.2, R630.1, R632.1
unnamed: J604.4, R631.1, R633.1
unnamed: LED601.2, R602.1
unnamed: R607.1, U601.L10 (VN_0)
unnamed: R608.1, U601.K9 (VP_0)
unnamed: R615.2, S601.1 (N+)
unnamed: R616.1, R617.1, Y602.4 (OUT)
unnamed: R634.1, U601.A5 (PS_MIO6_500)
unnamed: R635.2, U601.D14 (PS_MIO40_501)
unnamed: U1.A3 (VCCO_DDR_502), U1.D2 (VCCO_DDR_502)
OTG_CLK: U601.A11 (PS_MIO36_501)
OTG_DATA0: U601.A14 (PS_MIO32_501)
OTG_DATA1: U601.D15 (PS_MIO33_501)
OTG_DATA2: U601.A12 (PS_MIO34_501)
OTG_DATA3: U601.F12 (PS_MIO35_501)
OTG_DATA4: U601.C16 (PS_MIO28_501)
OTG_DATA5: U601.A10 (PS_MIO37_501)
OTG_DATA6: U601.E13 (PS_MIO38_501)
OTG_DATA7: U601.C18 (PS_MIO39_501)
OTG_DIR: U601.C13 (PS_MIO29_501)
OTG_NXT: U601.E16 (PS_MIO31_501)
OTG_OC: U601.C6 (PS_MIO11_500)
OTG_RESETN: U601.D16 (PS_MIO46_501)
OTG_STP: U601.C15 (PS_MIO30_501)
PG_ALL: U601.C7 (PS_POR_B_500)
PROGRAM_B: U601.L6 (PROGRAM_B_0)
PS_CLK: R616.2, U601.E7 (PS_CLK_500)
PS_RST: R614.2, R615.1, U601.B10 (PS_SRST_B_501), U603.3 (A2)
SD_CCLK: R635.1
SD_CD: U601.B14 (PS_MIO47_501)
SD_CMD: U601.C17 (PS_MIO41_501)
SD_D0: U601.E12 (PS_MIO42_501)
SD_D1: U601.A9 (PS_MIO43_501)
SD_D2: U601.F13 (PS_MIO44_501)
SD_D3: U601.B15 (PS_MIO45_501)
SPI_CS: R610.1, U601.A7 (PS_MIO1_500), U602.7 (*CS)
SPI_DQ0/MODE3: R632.2, U601.B8 (PS_MIO2_500), U602.15 (SI/IO0)
SPI_DQ1/MODE1: R629.2, U601.D6 (PS_MIO3_500), U602.8 (SO/IO1)
SPI_DQ2/MODE2: R622.2, U601.B7 (PS_MIO4_500), U602.9 (*WP/IO2)
SPI_DQ3/MODE0: R621.2, U601.A6 (PS_MIO5_500), U602.1 (*HOLD/IO3)
SPI_SCK/MODE4: R633.2, R634.2, U602.16 (SCK)
SPI_SCLK_FB/VCFG1: R627.2, U601.D5 (PS_MIO8_500)
TCK: R606.2, U601.F9 (TCK_0)
TDI_USB/TDO_FPGA: R605.2, U601.F6 (TDO_0)
TDO_USB/TDI_FPGA: R604.2, U601.G6 (TDI_0)
TMS: R603.2, U601.J6 (TMS_0)
UART_RXD_OUT: U601.C8 (PS_MIO15_500)
UART_TXD_IN: U601.C5 (PS_MIO14_500)
VCC1V0: C602.1, C605.1, C608.1, C610.1, C611.1, C612.1, C614.1, C617.1, C622.1, C627.1, C648.1, C649.1, C650.1, C652.1, C654.1, C657.1, U1.G7 (VCCPINT), U1.J7 (VCCPINT), U1.L7 (VCCPINT), U1.N7 (VCCPINT), U1.P8 (VCCPINT), U1.R7 (VCCPINT), U601.G11 (VCCBRAM), U601.G13 (VCCINT), U601.H10 (VCCBRAM), U601.H12 (VCCINT), U601.J13 (VCCINT), U601.K12 (VCCINT), U601.L13 (VCCINT), U601.M12 (VCCINT), U601.N13 (VCCINT), U601.P12 (VCCINT), U601.R13 (VCCINT)
VCC1V5: C613.1, C616.1, C626.1, C631.1, C635.1, C638.1, C642.1, R611.1, R623.1, U1.E5 (VCCO_DDR_502), U1.P2 (VCCO_DDR_502), U1.R5 (VCCO_DDR_502), U1.V4 (VCCO_DDR_502)
VCC1V8: C601.1, C604.1, C607.1, C615.1, C618.1, C623.1, C651.1, C653.1, C655.1, C656.1, FB1.2, R614.1, R625.1, U1.A13 (VCCO_MIO1_501), U1.B16 (VCCO_MIO1_501), U1.D12 (VCCO_MIO1_501), U1.E15 (VCCO_MIO1_501), U1.F8 (VCCPAUX), U1.G9 (VCCPAUX), U1.K8 (VCCPAUX), U1.M8 (VCCPAUX), U601.F11 (VCCBATT_0), U601.J9 (VCCADC_0), U601.J11 (VCCAUX), U601.L11 (VCCAUX), U601.N9 (VCCAUX), U601.N11 (VCCAUX), U601.P10 (VCCAUX), U601.R9 (VCCAUX)
VCC3V3: C1.1, C2.1, C3.1, C4.1, C5.1, C6.1, C7.1, C8.1, C9.1, C603.1, C606.1, C609.1, C647.1, C658.1, C659.1, C660.1, C661.1, C662.1, J602.1, J603.4, J604.1, R601.2, R609.2, R610.2, R618.1, R619.2, R627.1, U1.B6 (VCCO_MIO0_500), U1.D7 (VCCO_MIO0_500), U1.N19 (VCCO_34), U1.R15 (VCCO_34), U1.T8 (VCCO_13), U1.T18 (VCCO_34), U1.U11 (VCCO_13), U1.W7 (VCCO_13), U1.Y20 (VCCO_34), U601.K6 (VCCO_0), U601.M6 (CFGBVS_0), U601.N6 (RSVDVCC3), U601.R6 (RSVDVCC2), U601.T6 (RSVDVCC1), U602.2 (VCC), U603.5 (VCC), Y602.1 (EN), Y602.6 (VDD)
VCFG0: R628.2, U601.D8 (PS_MIO7_500)
VREF0V9: C667.1, C668.1, C669.1, C670.1, R625.2, R626.1, U601.E11 (PS_MIO_VREF_501)
XADCVREF: C645.1, U1.K10 (VREFN_0)
XADC_V_N: C646.1, R607.2
XADC_V_P: C646.2, R608.2

Notes on the sheet:
JTAG needs to be removed
Decoupling capacitors
