ee23btech11217/Prism/PCB/power.kicad_sch

## KiCad design PCB/power.kicad_sch (2025-03-10, last stored version)

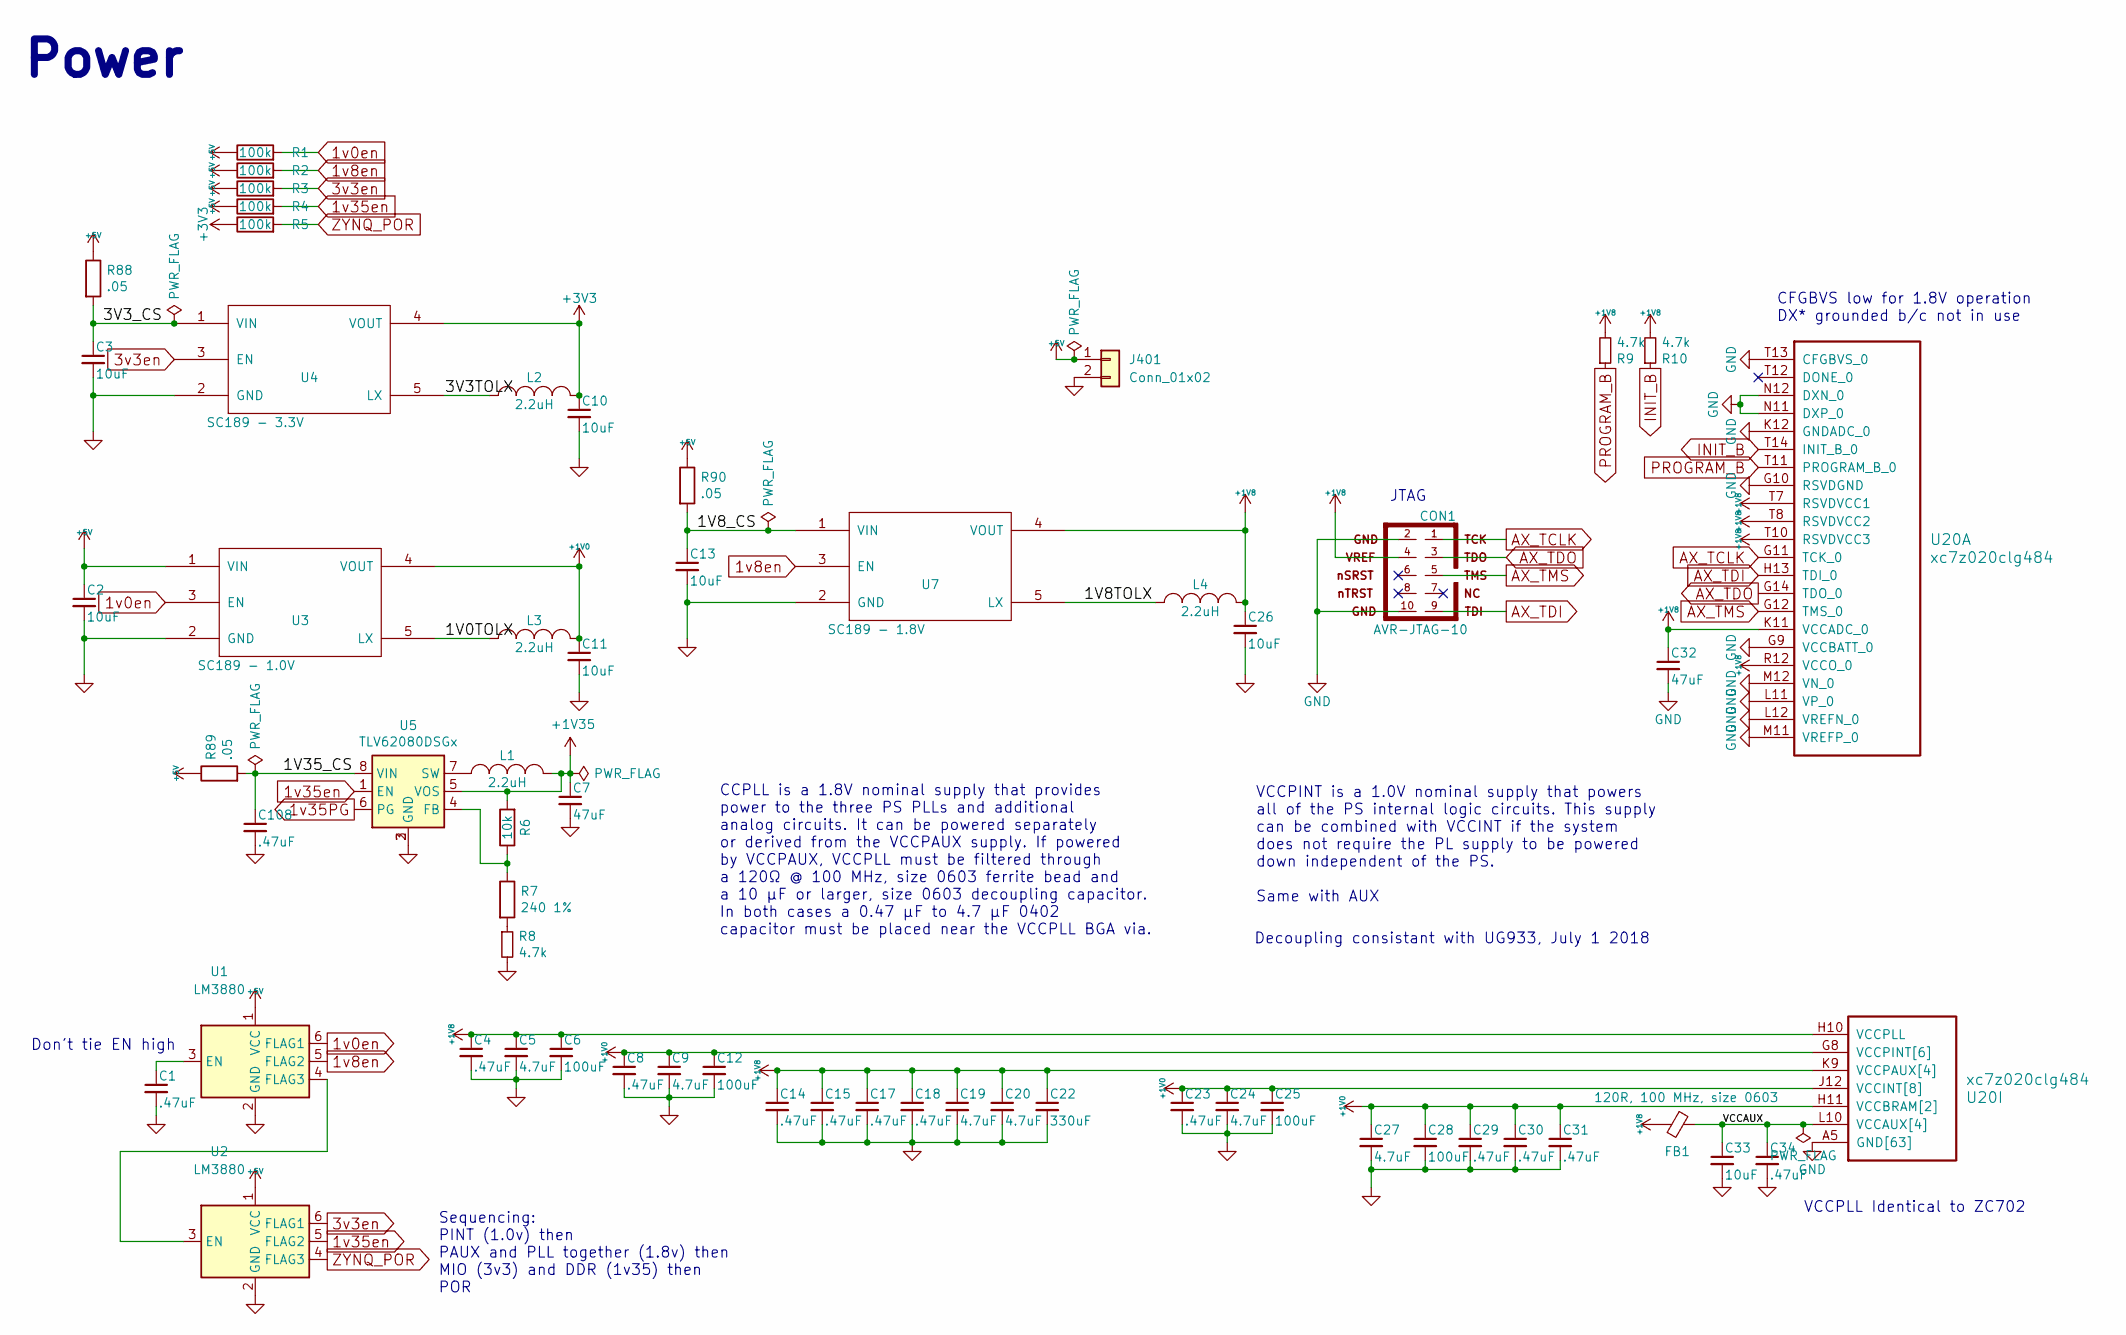
[picture p24: schematic power.kicad_sch]

Parts:
C1, C4, C8, C14, C15, C17, C18, C23, C29, C30, C31, C34, C108: .47uF; C_0402_1005Metric; MPN CC0402KRX5R5BB474
C2, C3, C10, C11, C13, C26, C33: 10uF; C_0603_1608Metric; MPN GRM188R61A106KE69J
C5, C9, C19, C20, C24, C27: 4.7uF; C_0402_1005Metric; MPN GRM155R60G475ME47D
C6, C12, C25, C28: 100uF; C_1210_3225Metric; MPN JMK325ABJ107MM-P
C7, C32: 47uF; C_0805_2012Metric; MPN GRM219R60J476ME44D
C22: 330uF; C_1206_3216Metric; MPN F950G337MAAAQ2
CON1: AVR-JTAG-10; XilinxJTAG
FB1: 120R, 100 MHz, size 0603; C_0603_1608Metric; MPN BLM18AG121SN1D
J401: Conn_01x02; PHOENIX_1748167
L1, L2, L3, L4: 2.2uH; C_1812_4532Metric; MPN LQH43PN2R2M26L
R1, R2, R3, R4, R5: 100k; R_0402_1005Metric; MPN RC0402FR-07100KL
R6: 10k; R_0402_1005Metric; MPN RC0402FR-0710KL
R7: 240 1%; R_0402_1005Metric; MPN RC0402FR-07240RL
R8, R9, R10: 4.7k; R_0402_1005Metric; MPN RC0402JR-074K7L
R88, R89, R90: .05; R_2512_6332Metric; MPN CRA2512-FZ-R050ELF
U1, U2: LM3880; SOT-23-6; MPN LM3880MF-1AE/NOPB
U3: SC189 - 1.0V; SOT-23-5; MPN SC189ASKTRT
U4: SC189 - 3.3V; SOT-23-5; MPN SC189ZSKTRT
U5: TLV62080DSGx; WSON-8-1EP_2x2mm_P0.5mm_EP0.9x1.6mm; MPN TLV62080DSGR
U7: SC189 - 1.8V; SOT-23-5; MPN SC189LSKTRT
U20: xc7z020clg484; BGA-484_19.0x19.0mm_Layout22x22_P0.80mm_dia0.40mm

Connections:
1V0TOLX: L3.1, U3.5 (LX)
1V8TOLX: L4.1, U7.5 (LX)
1V8_CS: C13.1, R90.2, U7.1 (VIN)
1V35_CS: C108.1, R89.2, U5.8 (VIN)
1v0en: R1.2, U1.6 (FLAG1), U3.3 (EN)
1v8en: R2.2, U1.5 (FLAG2), U7.3 (EN)
1v35PG: U5.6 (PG)
1v35en: R4.2, U2.5 (FLAG2), U5.1 (EN)
3V3TOLX: L2.1, U4.5 (LX)
3V3_CS: C3.1, R88.2, U4.1 (VIN)
3v3en: R3.2, U2.6 (FLAG1), U4.3 (EN)
+1V0: C8.1, C9.1, C11.1, C12.1, C23.1, C24.1, C25.1, C27.1, C28.1, C29.1, C30.1, C31.1, L3.2, U3.4 (VOUT), U20.G8 (VCCPINT[6]), U20.H9 (VCCPINT[6]), U20.H11 (VCCBRAM[2]), U20.J8 (VCCPINT[6]), U20.J10 (VCCBRAM[2]), U20.J12 (VCCINT[8]), U20.J14 (VCCINT[8]), U20.K13 (VCCINT[8]), U20.L8 (VCCPINT[6]), U20.L14 (VCCINT[8]), U20.M13 (VCCINT[8]), U20.N8 (VCCPINT[6]), U20.N14 (VCCINT[8]), U20.P13 (VCCINT[8]), U20.R8 (VCCPINT[6]), U20.R14 (VCCINT[8])
+1V8: C4.1, C5.1, C6.1, C14.1, C15.1, C17.1, C18.1, C19.1, C20.1, C22.1, C26.1, C32.1, CON1.4, FB1.2, L4.2, R9.2, R10.2, U7.4 (VOUT), U20.H10 (VCCPLL), U20.K9 (VCCPAUX[4]), U20.K11 (VCCADC_0), U20.M9 (VCCPAUX[4]), U20.P9 (VCCPAUX[4]), U20.R12 (VCCO_0), U20.T7 (RSVDVCC1), U20.T8 (RSVDVCC2), U20.T9 (VCCPAUX[4]), U20.T10 (RSVDVCC3)
+1V35: C7.1, L1.2, R6.2, U5.5 (VOS)
+3V3: C10.1, L2.2, R5.1, U4.4 (VOUT)
+5V: C2.1, J401.1, R1.1, R2.1, R3.1, R4.1, R88.1, R89.1, R90.1, U1.1 (VCC), U2.1 (VCC), U3.1 (VIN)
AX_TCLK: CON1.1, U20.G11 (TCK_0)
AX_TDI: CON1.9, U20.H13 (TDI_0)
AX_TDO: CON1.3, U20.G14 (TDO_0)
AX_TMS: CON1.5, U20.G12 (TMS_0)
GND: C1.2, C2.2, C3.2, C4.2, C5.2, C6.2, C7.2, C8.2, C9.2, C10.2, C11.2, C12.2, C13.2, C14.2, C15.2, C17.2, C18.2, C19.2, C20.2, C22.2, C23.2, C24.2, C25.2, C26.2, C27.2, C28.2, C29.2, C30.2, C31.2, C32.2, C33.2, C34.2, C108.2, CON1.2, CON1.10, J401.2, R8.2, U1.2 (GND), U2.2 (GND), U3.2 (GND), U4.2 (GND), U5.2 (GND), U5.3 (GND), U5.9 (GND), U7.2 (GND), U20.A5 (GND[63]), U20.A15 (GND[63]), U20.AA5 (GND[63]), U20.AA15 (GND[63]), U20.AB8 (GND[63]), U20.AB18 (GND[63]), U20.B8 (GND[63]), U20.B18 (GND[63]), U20.C1 (GND[63]), U20.C11 (GND[63]), U20.C21 (GND[63]), U20.D4 (GND[63]), U20.D14 (GND[63]), U20.E7 (GND[63]), U20.E17 (GND[63]), U20.F10 (GND[63]), U20.F20 (GND[63]), U20.G3 (GND[63]), U20.G9 (VCCBATT_0), U20.G10 (RSVDGND), U20.H6 (GND[63]), U20.H8 (GND[63]), U20.H12 (GND[63]), U20.H14 (GND[63]), U20.H16 (GND[63]), U20.J9 (GND[63]), U20.J11 (GND[63]), U20.J13 (GND[63]), U20.J19 (GND[63]), U20.K2 (GND[63]), U20.K8 (GND[63]), U20.K10 (GND[63]), U20.K12 (GNDADC_0), U20.K14 (GND[63]), U20.K22 (GND[63]), U20.L5 (GND[63]), U20.L9 (GND[63]), U20.L11 (VP_0), U20.L12 (VREFN_0), U20.L13 (GND[63]), U20.L15 (GND[63]), U20.M8 (GND[63]), U20.M10 (GND[63]), U20.M11 (VREFP_0), U20.M12 (VN_0), U20.M14 (GND[63]), U20.M18 (GND[63]), U20.N1 (GND[63]), U20.N9 (GND[63]), U20.N11 (DXP_0), U20.N12 (DXN_0), U20.N13 (GND[63]), U20.N21 (GND[63]), U20.P4 (GND[63]), U20.P8 (GND[63]), U20.P10 (GND[63]), U20.P12 (GND[63]), U20.P14 (GND[63]), U20.R9 (GND[63]), U20.R11 (GND[63]), U20.R13 (GND[63]), U20.R17 (GND[63]), U20.T13 (CFGBVS_0), U20.T20 (GND[63]), U20.U3 (GND[63]), U20.U13 (GND[63]), U20.V6 (GND[63]), U20.V16 (GND[63]), U20.W9 (GND[63]), U20.W19 (GND[63]), U20.Y2 (GND[63]), U20.Y12 (GND[63]), U20.Y22 (GND[63])
INIT_B: R10.1, U20.T14 (INIT_B_0)
unnamed: C1.1, U1.3 (EN)
unnamed: L1.1, U5.7 (SW)
unnamed: R6.1, R7.1, U5.4 (FB)
unnamed: R7.2, R8.1
unnamed: U1.4 (FLAG3), U2.3 (EN)
PROGRAM_B: R9.1, U20.T11 (PROGRAM_B_0)
VCCAUX: C33.1, C34.1, FB1.1, U20.L10 (VCCAUX[4]), U20.N10 (VCCAUX[4]), U20.P11 (VCCAUX[4]), U20.R10 (VCCAUX[4])
ZYNQ_POR: R5.2, U2.4 (FLAG3)

Notes on the sheet:
Decoupling consistant with UG933, July 1 2018
Power
VCCPLL Identical to ZC702
CCPLL is a 1.8V nominal supply that provides power to the three PS PLLs and additional analog circuits. It can be powered separately or derived from the VCCPAUX supply. If powered by VCCPAUX, VCCPLL must be filtered through a 120Ω @ 100 MHz, size 0603 ferrite bead and a 10 µF or larger, size 0603 d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
VCCPINT is a 1.0V nominal supply that powers all of the PS internal logic circuits. This supply can be combined with VCCINT if the system does not require the PL supply to be powered down independent of the PS. Same with AUX
CFGBVS low for 1.8V operation DX* grounded b/c not in use
Sequencing: PINT (1.0v) then PAUX and PLL together (1.8v) then MIO (3v3) and DDR (1v35) then POR
Don't tie EN high
JTAG
