ee23btech11217/Prism/PCB/prism-audio.kicad_sch

## KiCad design PCB/prism-audio.kicad_sch (2025-03-09, last stored version)

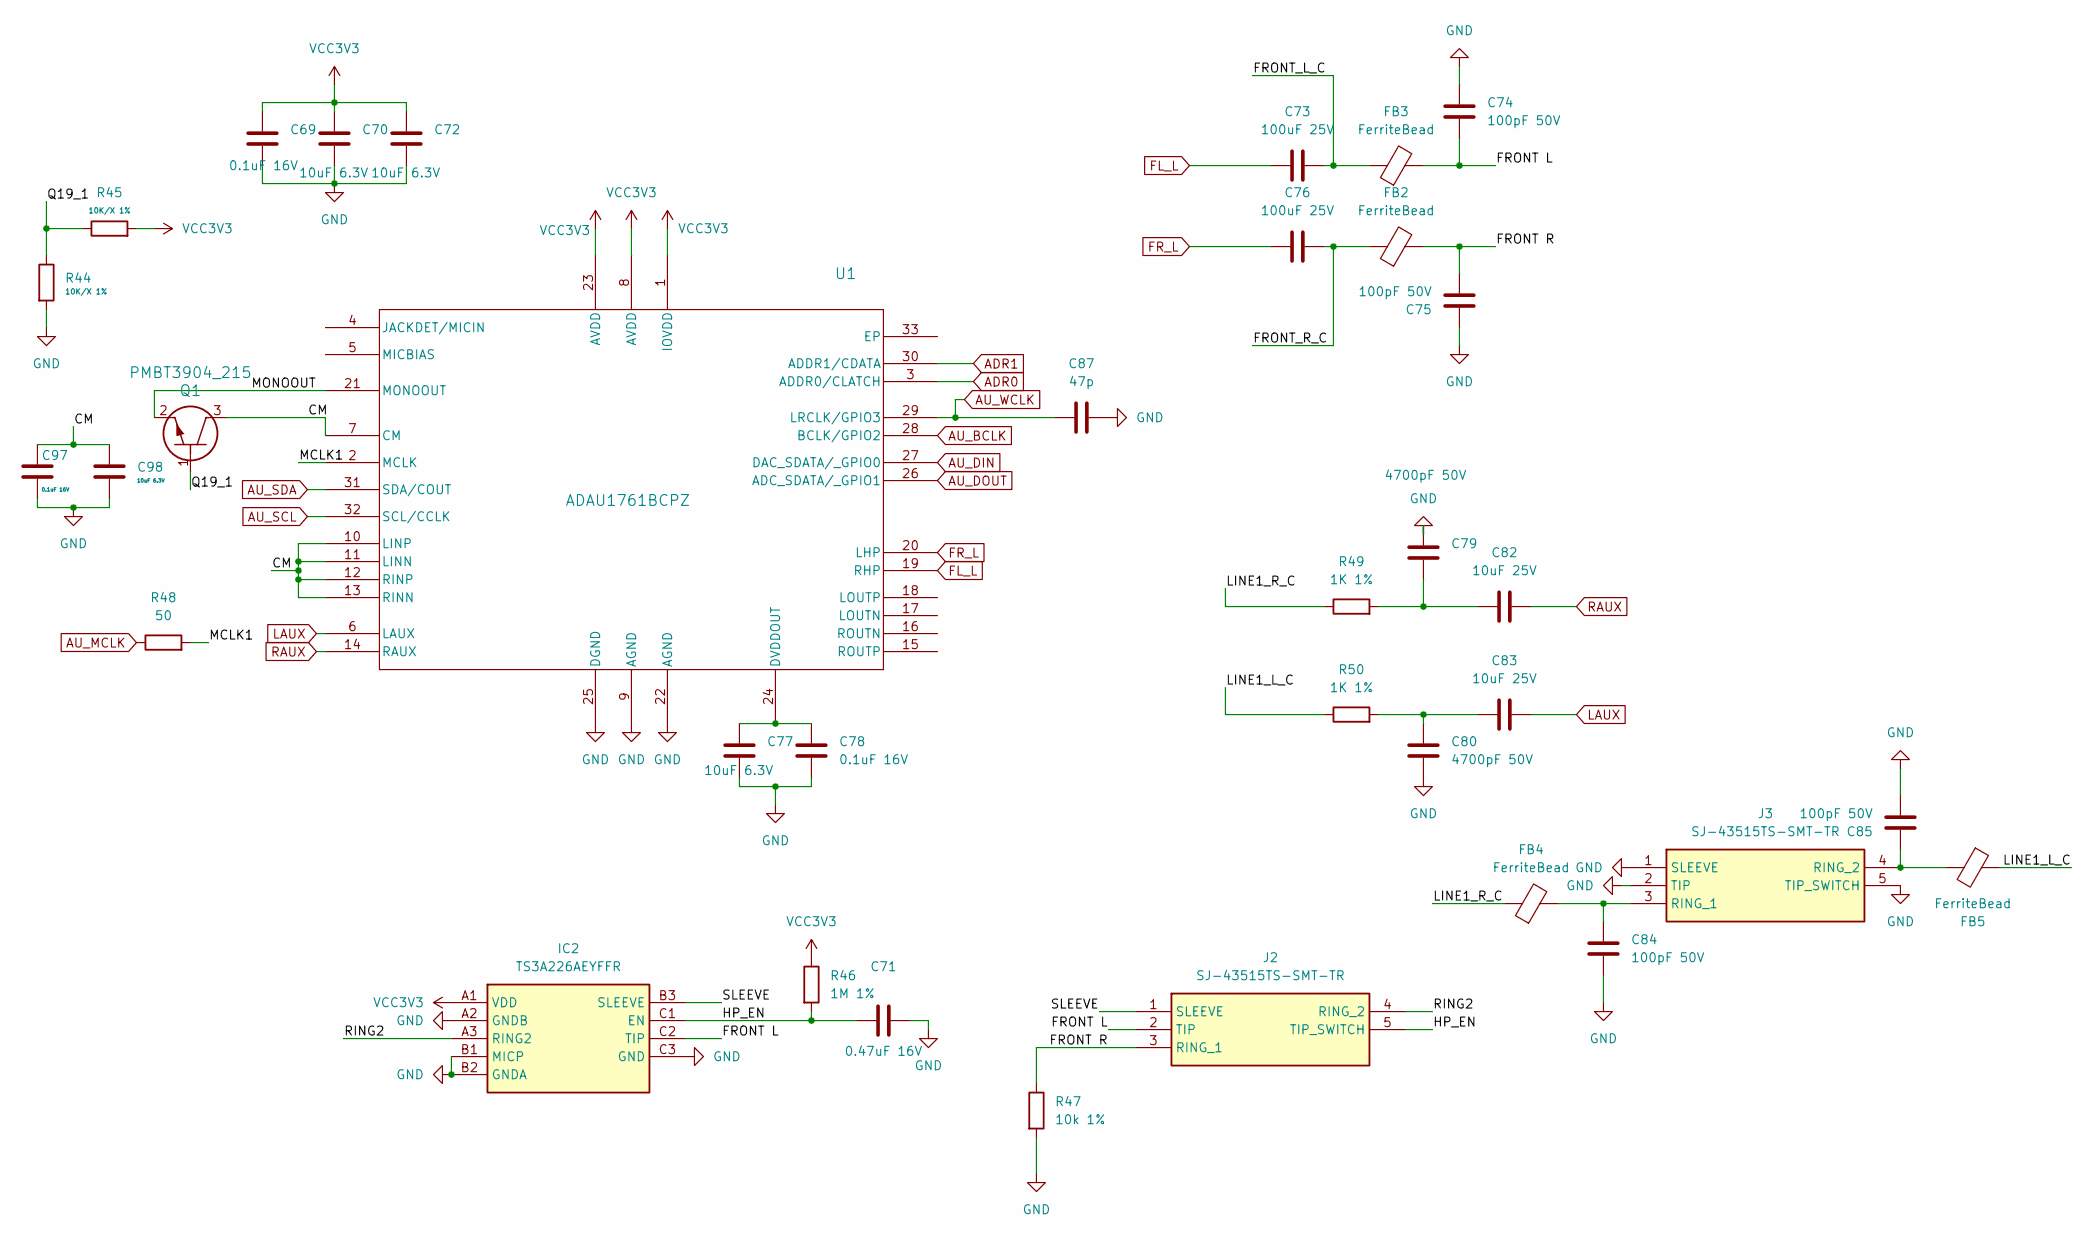
[picture p25: schematic prism-audio.kicad_sch]

Parts:
C69, C78, C97: 0.1uF 16V
C70, C72, C77, C98: 10uF 6.3V
C71: 0.47uF 16V
C73, C76: 100uF 25V
C74, C75, C84, C85: 100pF 50V
C79, C80: 4700pF 50V
C82, C83: 10uF 25V
C87: 47p
FB2, FB3, FB4, FB5: FerriteBead; L_0805_2012Metric
IC2: TS3A226AEYFFR; BGA9C40P3X3_126X136X62; Mouser Part Number 595-TS3A226AEYFFR
J2, J3: SJ-43515TS-SMT-TR; SJ43515TSSMTTR; Mouser Part Number 490-SJ43515TS-SMT-TR
Q1: PMBT3904_215; SOT23_TO-236AB_NEX
R44, R45: 10K/X 1%
R46: 1M 1%
R47: 10k 1%
R48: 50
R49, R50: 1K 1%; R_0603_1608Metric
U1: ADAU1761BCPZ; CP-32-4_ADI

Connections:
ADR0: U1.3 (ADDR0/CLATCH)
ADR1: U1.30 (ADDR1/CDATA)
AU_BCLK: U1.28 (BCLK/GPIO2)
AU_DIN: U1.27 (DAC_SDATA/_GPIO0)
AU_DOUT: U1.26 (ADC_SDATA/_GPIO1)
AU_MCLK: R48.1
AU_SCL: U1.32 (SCL/CCLK)
AU_SDA: U1.31 (SDA/COUT)
AU_WCLK: C87.1, U1.29 (LRCLK/GPIO3)
CM: C97.1, C98.1, Q1.3, U1.7 (CM), U1.10 (LINP), U1.11 (LINN), U1.12 (RINP), U1.13 (RINN)
FL_L: C73.1, U1.19 (RHP)
FRONT L: C74.2, FB3.2, IC2.C2 (TIP), J2.2 (TIP)
FRONT R: C75.2, FB2.2, J2.3 (RING_1), R47.1
FRONT_L_C: C73.2, FB3.1
FRONT_R_C: C76.2, FB2.1
FR_L: C76.1, U1.20 (LHP)
GND: C69.2, C70.2, C71.2, C72.2, C74.1, C75.1, C77.2, C78.2, C79.1, C80.2, C84.2, C85.2, C87.2, C97.2, C98.2, IC2.A2 (GNDB), IC2.B1 (MICP), IC2.B2 (GNDA), IC2.C3 (GND), J3.1 (SLEEVE), J3.2 (TIP), J3.5 (TIP_SWITCH), R44.2, R47.2, U1.9 (AGND), U1.22 (AGND), U1.25 (DGND)
HP_EN: C71.1, IC2.C1 (EN), J2.5 (TIP_SWITCH), R46.2
LAUX: C83.2, U1.6 (LAUX)
LINE1_L_C: FB5.1, R50.1
LINE1_R_C: FB4.1, R49.1
MCLK1: R48.2, U1.2 (MCLK)
MONOOUT: Q1.2, U1.21 (MONOOUT)
unnamed: C77.1, C78.1, U1.24 (DVDDOUT)
unnamed: C79.2, C82.1, R49.2
unnamed: C80.1, C83.1, R50.2
unnamed: C84.1, FB4.2, J3.3 (RING_1)
unnamed: C85.1, FB5.2, J3.4 (RING_2)
Q19_1: Q1.1, R44.1, R45.1
RAUX: C82.2, U1.14 (RAUX)
RING2: IC2.A3 (RING2), J2.4 (RING_2)
SLEEVE: IC2.B3 (SLEEVE), J2.1 (SLEEVE)
VCC3V3: C69.1, C70.1, C72.1, IC2.A1 (VDD), R45.2, R46.1, U1.1 (IOVDD), U1.8 (AVDD), U1.23 (AVDD)
