ee23btech11217/Prism/PCB/sd.kicad_sch

## KiCad design PCB/sd.kicad_sch (2025-03-01, last stored version)

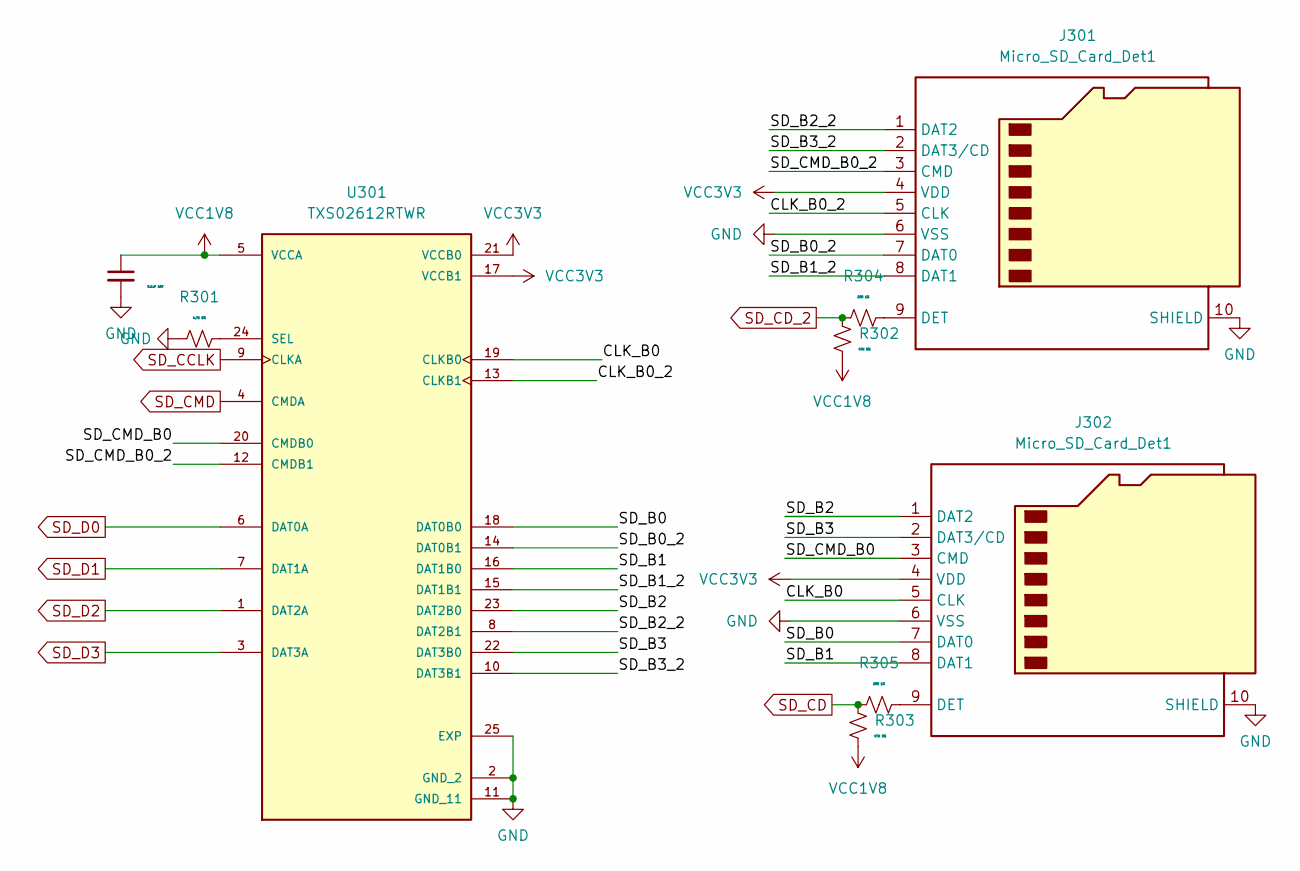
[picture p26: schematic sd.kicad_sch]

Parts:
C301: 0.1uF 16V
J301, J302: Micro_SD_Card_Det1
R301: 4.7K 5%; R_0805_2012Metric
R302, R303: 47K 5%; R_0805_2012Metric
R304, R305: 200 1%; R_0805_2012Metric
U301: TXS02612RTWR; QFN50P400X400X80-25N; PARTREV 4219135/B 11/2016

Connections:
CLK_B0: J302.5 (CLK), U301.19 (CLKB0)
CLK_B0_2: J301.5 (CLK), U301.13 (CLKB1)
GND: C301.2, J301.6 (VSS), J301.10 (SHIELD), J302.6 (VSS), J302.10 (SHIELD), R301.1, U301.2 (GND_2), U301.11 (GND_11), U301.25 (EXP)
unnamed: J301.9 (DET), R304.2
unnamed: J302.9 (DET), R305.2
unnamed: R301.2, U301.24 (SEL)
SD_B0: J302.7 (DAT0), U301.18 (DAT0B0)
SD_B0_2: J301.7 (DAT0), U301.14 (DAT0B1)
SD_B1: J302.8 (DAT1), U301.16 (DAT1B0)
SD_B1_2: J301.8 (DAT1), U301.15 (DAT1B1)
SD_B2: J302.1 (DAT2), U301.23 (DAT2B0)
SD_B2_2: J301.1 (DAT2), U301.8 (DAT2B1)
SD_B3: J302.2 (DAT3/CD), U301.22 (DAT3B0)
SD_B3_2: J301.2 (DAT3/CD), U301.10 (DAT3B1)
SD_CCLK: U301.9 (CLKA)
SD_CD: R303.1, R305.1
SD_CD_2: R302.1, R304.1
SD_CMD: U301.4 (CMDA)
SD_CMD_B0: J302.3 (CMD), U301.20 (CMDB0)
SD_CMD_B0_2: J301.3 (CMD), U301.12 (CMDB1)
SD_D0: U301.6 (DAT0A)
SD_D1: U301.7 (DAT1A)
SD_D2: U301.1 (DAT2A)
SD_D3: U301.3 (DAT3A)
VCC1V8: C301.1, R302.2, R303.2, U301.5 (VCCA)
VCC3V3: J301.4 (VDD), J302.4 (VDD), U301.17 (VCCB1), U301.21 (VCCB0)
