ee23btech11217/Prism/PCB/sensors.kicad_sch

## KiCad design PCB/sensors.kicad_sch (2025-03-01, last stored version)

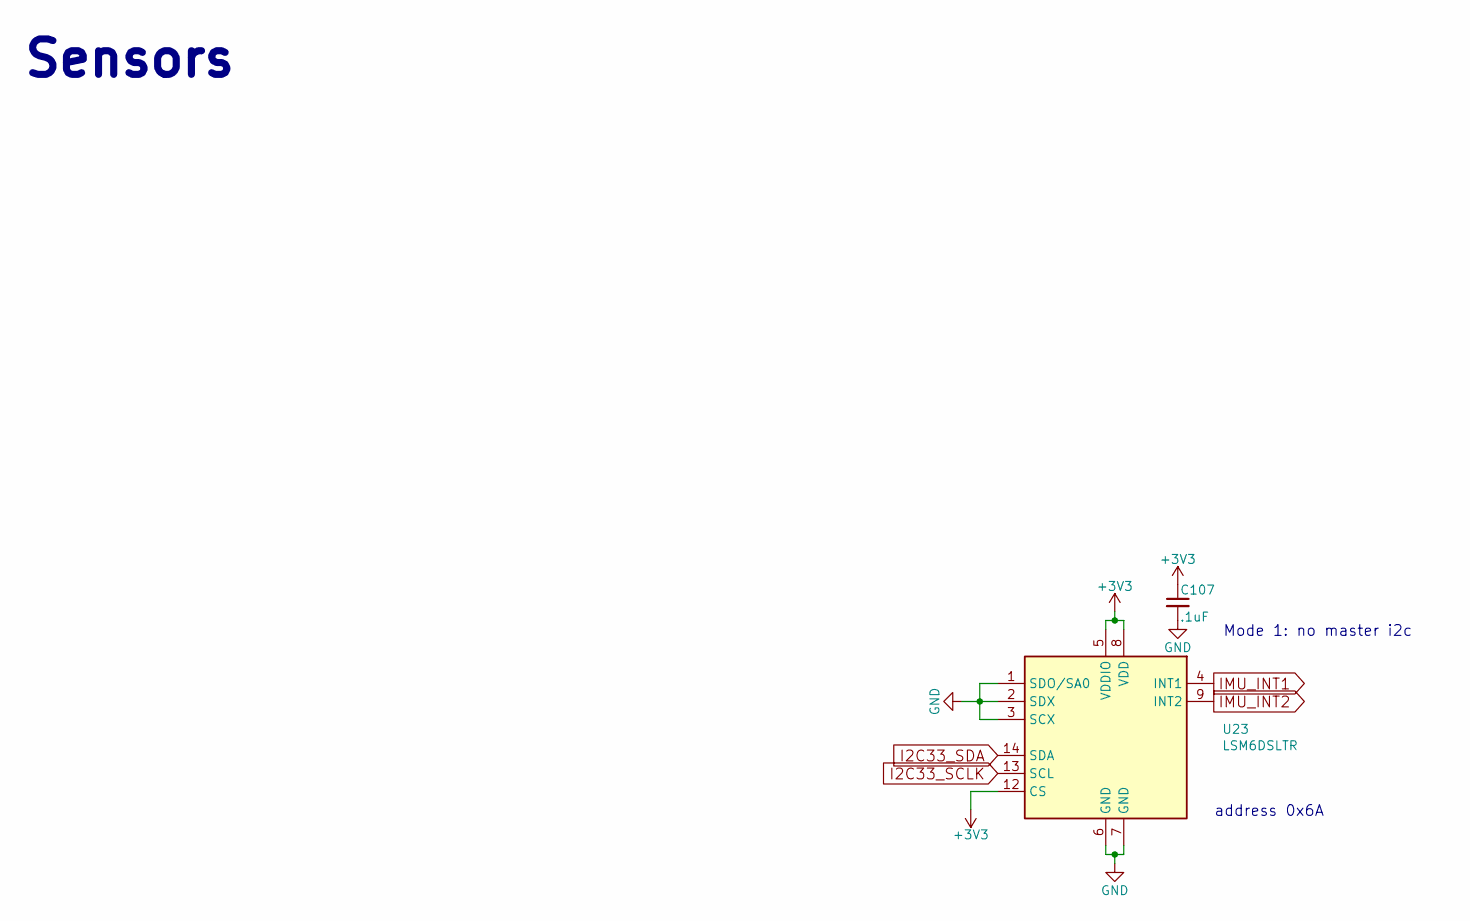
[picture p27: schematic sensors.kicad_sch]

Parts:
C107: .1uF; C_0402_1005Metric; MPN CC0402KRX7R6BB104
U23: LSM6DSLTR; LGA-14_3x2.5mm_P0.5mm_LayoutBorder3x4y; MPN LSM6DSLTR

Connections:
+3V3: C107.1, U23.5 (VDDIO), U23.8 (VDD), U23.12 (CS)
GND: C107.2, U23.1 (SDO/SA0), U23.2 (SDX), U23.3 (SCX), U23.6 (GND), U23.7 (GND)
I2C33_SCLK: U23.13 (SCL)
I2C33_SDA: U23.14 (SDA)
IMU_INT1: U23.4 (INT1)
IMU_INT2: U23.9 (INT2)

Notes on the sheet:
address 0x6A
Sensors
Mode 1: no master i2c
